fenrir-naru/ninja-scan-light/board/NinjaScanLight2-layout_BOM.png

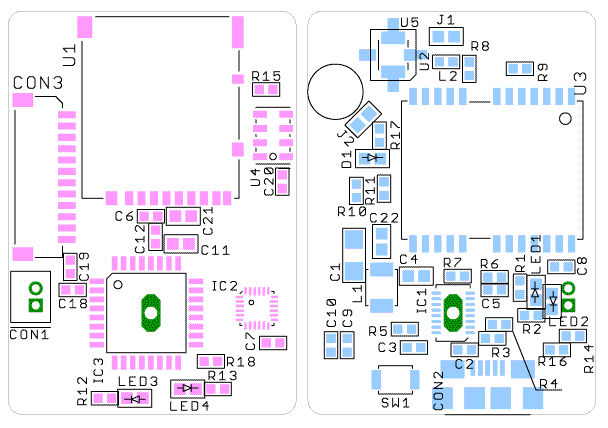
board/NinjaScanLight2-layout_BOM.png
