fenrir-naru/ninja-scan-light/board/NinjaScanLight-layout_BOM.png

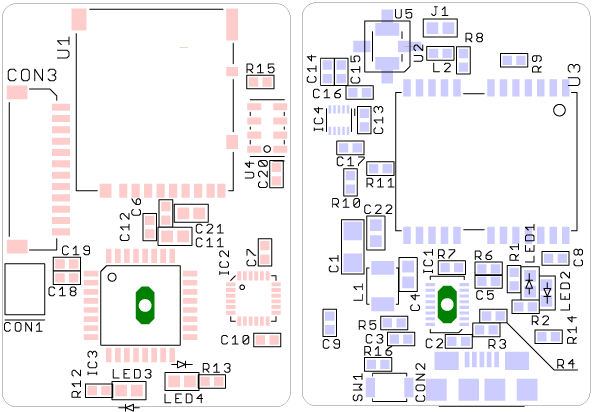
board/NinjaScanLight-layout_BOM.png
