fenrir-naru/ninja-scan-light/board/NinjaScanSlim-layout_BOM.png

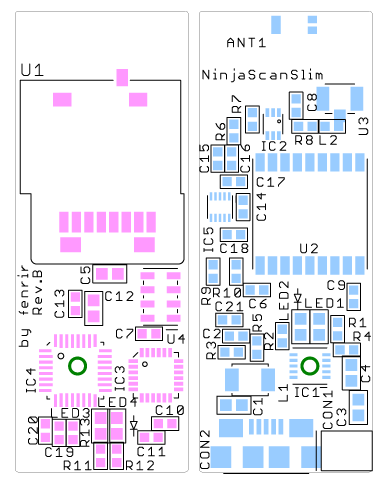
board/NinjaScanSlim-layout_BOM.png
