fenrir-naru/ninja-scan-light/firmware/f38x_uart0.c

/*
 * Copyright (c) 2013, M.Naruoka (fenrir)
 * All rights reserved.
 * 
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
 * THIS SOFTWARE IS PROVIDED BY THE COPYRIGHT HOLDERS AND CONTRIBUTORS "AS IS" 
 * AND ANY EXPRESS OR IMPLIED WARRANTIES, INCLUDING, BUT NOT LIMITED TO, 
 * THE IMPLIED WARRANTIES OF MERCHANTABILITY AND FITNESS FOR A PARTICULAR PURPOSE 
 * ARE DISCLAIMED. IN NO EVENT SHALL THE COPYRIGHT HOLDER OR CONTRIBUTORS 
 * BE LIABLE FOR ANY DIRECT, INDIRECT, INCIDENTAL, SPECIAL, EXEMPLARY, 
 * OR CONSEQUENTIAL DAMAGES (INCLUDING, BUT NOT LIMITED TO, 
 * PROCUREMENT OF SUBSTITUTE GOODS OR SERVICES; 
 * LOSS OF USE, DATA, OR PROFITS; OR BUSINESS INTERRUPTION) 
 * HOWEVER CAUSED AND ON ANY THEORY OF LIABILITY, WHETHER IN CONTRACT, 
 * STRICT LIABILITY, OR TORT (INCLUDING NEGLIGENCE OR OTHERWISE) 
 * ARISING IN ANY WAY OUT OF THE USE OF THIS SOFTWARE, 
 * EVEN IF ADVISED OF THE POSSIBILITY OF SUCH DAMAGE.
 * 
 */

#include <stdio.h>

#include "main.h"
#include "f38x_uart0.h"
#include "fifo.h"

#define DEFAULT_BAUDRATE     9600UL  // Baud rate of UART in bps

#define CRITICAL_UART0(func) \
{\
  ES0 = 0;\
  func;\
  ES0 = 1;\
}

__xdata fifo_char_t fifo_tx0; ///< FIFO TX
__xdata fifo_char_t fifo_rx0; ///< FIFO RX
static __xdata __at (0x000) 
  char buffer_tx0[UART0_TX_BUFFER_SIZE];
static __xdata __at (0x000 + UART0_TX_BUFFER_SIZE) 
  char buffer_rx0[UART0_RX_BUFFER_SIZE];

/**
 * Change UART0 baudrate
 */
static void uart0_bauding_config(u16 baudrate_register){
  
  TR1 = 0;
  do{
    if (baudrate_register < 0x100){
      TH1 = (u8)(~baudrate_register);
      CKCON |=  0x08;  // T1M = 1; SCA1:0 = xx
      break;
    }
    baudrate_register >>= 2; // 1/4
    if (baudrate_register < 0x100){
      TH1 = (u8)(~baudrate_register);
      CKCON &= ~0x0B;
      CKCON |=  0x01;  // T1M = 0; SCA1:0 = 01
      break;
    }
    baudrate_register /= 3; // 1/4*1/3=1/12
    if (baudrate_register < 0x100){
      TH1 = (u8)(~baudrate_register);
      CKCON &= ~0x0B;  // T1M = 0; SCA1:0 = 00
      break;
    }
    baudrate_register >>= 2; // 1/4*1/3*1/4=1/48
    TH1 = (u8)(~baudrate_register);
    CKCON &= ~0x0B;
    CKCON |=  0x02;    // T1M = 0; SCA1:0 = 10
  }while(0);
  
  TL1 = TH1;        // init Timer1
  TMOD &= ~0xf0;    // TMOD: timer 1 in 8-bit autoreload
  TMOD |=  0x20;
  TR1 = 1;
}

#define _uart0_bauding(baudrate, clk) \
  uart0_bauding_config((u16)(clk/2/baudrate))

void uart0_bauding(u32 baudrate){
  _uart0_bauding(baudrate, SYSCLK);
}

/**
 * Initialize UART0
 */
void uart0_init() {
  SCON0 = 0x10;     // SCON0: 8-bit variable bit rate
                    //        level of STOP bit is ignored
                    //        RX enabled
                    //        ninth bits are zeros
                    //        clear RI0 and TI0 bits
  fifo_char_init(&fifo_tx0, buffer_tx0, UART0_TX_BUFFER_SIZE); 
  fifo_char_init(&fifo_rx0, buffer_rx0, UART0_RX_BUFFER_SIZE); 

  _uart0_bauding(DEFAULT_BAUDRATE, SYSCLK);

  TB80 = 0;         // TB80 is used for writing flag. '1' means writing, otherwise '0'.
  ES0 = 1;          // Enable interrupt
  //PS0 = 1;          // Interrupt priority
}

void uart0_init_boot() {
  SCON0 = 0x10;     // SCON0: 8-bit variable bit rate
                    //        level of STOP bit is ignored
                    //        RX enabled
                    //        ninth bits are zeros
                    //        clear RI0 and TI0 bits
  _uart0_bauding(DEFAULT_BAUDRATE, SYSCLK_BOOT);
}

/**
 * Register transmitting data via UART0
 * 
 * @param data pointer to data
 * @param size size of data
 * @return (FIFO_SIZE_T) the size of registered data to buffer
 */
FIFO_SIZE_T uart0_write(char *buf, FIFO_SIZE_T size){
  if(size){
    if(ES0){ // non blocking
      // TB80 is used for writing flag.
      // if '0', which indicates not writing, interrupt must be invoked manually.
      size = fifo_char_write(&fifo_tx0, buf, size);
      CRITICAL_UART0(
        if(!(SCON0 & 0x0A)){ // !TB80 && !TI0
          TI0 = 1; // Manual interrupt
        }
      );
    }else{ // blocking
      FIFO_SIZE_T i = size;
      do{
        SBUF0 = *(buf++);
        while(!TI0);
        TI0 = 0;
      }while(--i);
    }
  }
  return size;
}

/**
 * Return the empty buffer size of data which will be transferred via UART0
 * 
 * @return (FIFO_SIZE_T) the size
 */
FIFO_SIZE_T uart0_tx_margin(){
  return fifo_char_margin(&fifo_tx0);
}

/**
 * Get the received data via UART0
 * 
 * @param buf buffer
 * @param size the size of buffer
 * @return (FIFO_SIZE_T) the real size of grabbed data
 */
FIFO_SIZE_T uart0_read(char *buf, FIFO_SIZE_T size){
  return fifo_char_read(&fifo_rx0, buf, size);
}

/**
 * Return the size of unread data which is received via UART0
 * 
 * @return (FIFO_SIZE_T) the size
 */
FIFO_SIZE_T uart0_rx_size(){
  return fifo_char_size(&fifo_rx0);
}

///< Interrupt(TI0 / RI0)
void interrupt_uart0 () __interrupt (INTERRUPT_UART0) {
  unsigned char res;

  if(RI0){
    RI0 = 0;
    /* push to ring buffer */
    FIFO_DIRECT_PUT(fifo_rx0, SBUF0, res);
    if(res == 0){
      // TODO: buffer overflow
    }
  }

  if(TI0){
    TI0 = 0;
    /* has byte to write? */
    FIFO_DIRECT_GET(fifo_tx0, SBUF0, res);
    if(res > 0){
      TB80 = 1; // TB80 is used as UART0 writing flag. set 1 (writing)
    }else{
      TB80 = 0; // TB80 is used as UART0 writing flag. set 0 (not writing)
    }
  }
}


// stdio.h support

/**
 * putchar - blocking
 */
#if defined(SDCC) && (SDCC >= 370)
int putchar (int c_){
  char c = (char)c_;
#else
void putchar (char c){
#endif
  while(uart0_write(&c, 1) == 0);
}

/**
 * getchar - blocking
 */
#if defined(SDCC) && (SDCC >= 370)
int getchar (void){
#else
char getchar (void){
#endif
  char c;
  while(uart0_read(&c, sizeof(c)) == 0);
  return c;
}
