fenrir-naru/ninja-scan-light/tool/log_CSV.cpp

/*
 * Copyright (c) 2013, M.Naruoka (fenrir)
 * All rights reserved.
 *
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
 * THIS SOFTWARE IS PROVIDED BY THE COPYRIGHT HOLDERS AND CONTRIBUTORS "AS IS"
 * AND ANY EXPRESS OR IMPLIED WARRANTIES, INCLUDING, BUT NOT LIMITED TO,
 * THE IMPLIED WARRANTIES OF MERCHANTABILITY AND FITNESS FOR A PARTICULAR PURPOSE
 * ARE DISCLAIMED. IN NO EVENT SHALL THE COPYRIGHT HOLDER OR CONTRIBUTORS
 * BE LIABLE FOR ANY DIRECT, INDIRECT, INCIDENTAL, SPECIAL, EXEMPLARY,
 * OR CONSEQUENTIAL DAMAGES (INCLUDING, BUT NOT LIMITED TO,
 * PROCUREMENT OF SUBSTITUTE GOODS OR SERVICES;
 * LOSS OF USE, DATA, OR PROFITS; OR BUSINESS INTERRUPTION)
 * HOWEVER CAUSED AND ON ANY THEORY OF LIABILITY, WHETHER IN CONTRACT,
 * STRICT LIABILITY, OR TORT (INCLUDING NEGLIGENCE OR OTHERWISE)
 * ARISING IN ANY WAY OUT OF THE USE OF THIS SOFTWARE,
 * EVEN IF ADVISED OF THE POSSIBILITY OF SUCH DAMAGE.
 *
 */

#if defined(_MSC_VER) && _MSC_VER >= 1400
#define _USE_MATH_DEFINES
//#define _CRT_SECURE_NO_WARNINGS // stop warning recommending secure functions such as sprintf_s
typedef __int64 int64_t;
#endif

#include <iostream>
#include <fstream>
#include <iomanip>
#include <sstream>
#include <exception>

#define IS_LITTLE_ENDIAN 1
#include "SylphideStream.h"
#include "SylphideProcessor.h"

typedef double float_sylph_t;
#include "analyze_common.h"
#include "calibration.h"

using namespace std;

struct Options : public GlobalOptions<float_sylph_t> {
  typedef GlobalOptions<float_sylph_t> super_t;
  enum {
    PAGE_A, PAGE_G, PAGE_F, PAGE_P, PAGE_M, PAGE_N, PAGE_OTHER,
    PAGE_KINDS
  };
  typedef enum {
    PAGE_SELECTED_POSITIVE = 1,
    PAGE_SELECTED_DEFAULT = 0,
    PAGE_SELECTED_NEGATIVE = -1,
  } page_selected_t;
  page_selected_t page_selected[PAGE_KINDS]; // = {PAGE_SELECTED_DEFAULT};

  int page_P_mode, page_F_mode, page_M_mode;
  int debug_level;
  typedef CalendarTime<float_sylph_t> calendar_time_t;
  calendar_time_t::Converter time_gps2local;
  bool use_calendar_time;
  bool as_filter;

  typedef StandardCalibration<float_sylph_t> inertial_conv_t;

  struct {
    bool is_active;
    inertial_conv_t inertial_conv;
  } physical_converter;

  Options() 
      : super_t(),
      page_P_mode(5),
      page_F_mode(3),
      page_M_mode(0),
      debug_level(0),
      time_gps2local(),
      use_calendar_time(false), as_filter(false) {

    physical_converter.is_active = false;
    super_t::set_typical_calibration_specs(physical_converter.inertial_conv);

    for(int i(0); i < PAGE_KINDS; ++i){
      page_selected[i] = PAGE_SELECTED_DEFAULT;
    }
  }
  ~Options(){}
  
  struct formatted_time_t {
    const Options &options;
    float_sylph_t itow;
    friend ostream &operator<<(ostream &out, const formatted_time_t &t){
      if(t.options.use_calendar_time){ // year, month, mday, hour, min, sec
        calendar_time_t t2(
            t.options.time_gps2local.convert(t.itow));
        out << t2.year << ", "
            << t2.month << ", "
            << t2.mday << ", "
            << t2.hour << ", "
            << t2.min << ", "
            << t2.sec;
      }else{
        out << t.itow;
      }
      return out;
    }
  };

  template <class T>
  formatted_time_t format_time(const T &itow){
    formatted_time_t res = {*this, itow};
    return res;
  }

  template <class T>
  bool is_time_in_range(const T &sec) const {
    return super_t::is_time_in_range(sec, time_gps2local.gps_time.wn);
  }
  bool is_time_in_range() const {
    return super_t::is_time_in_range(time_gps2local.gps_time.sec, time_gps2local.gps_time.wn);
  }

  /**
   * Check command argument
   * 
   * @param spec Command
   * @return (bool) If recognized, true; otherwise false
   */
  bool check_spec(const char *spec){
#define CHECK_OPTION(name, novalue, operation, disp) { \
  const char *value(get_value(spec, #name, novalue)); \
  if(value){ \
    {operation;} \
    std::cerr << #name << ": " << disp << std::endl; \
    return true; \
  } \
}
    CHECK_OPTION(page_P_mode, false,
        page_P_mode = atoi(value),
        page_P_mode);
    CHECK_OPTION(page_F_mode, false,
        page_F_mode = atoi(value),
        page_F_mode);
    CHECK_OPTION(page_M_mode, false,
        page_M_mode = atoi(value),
        page_M_mode);
    CHECK_OPTION(page_other, true,
        page_selected[PAGE_OTHER] = is_true(value) ? PAGE_SELECTED_POSITIVE : PAGE_SELECTED_NEGATIVE,
        (page_selected[PAGE_OTHER] > PAGE_SELECTED_DEFAULT ? "on" : "off"));

    do{ // Change time outputs from gpstime[ms] to calendartime(YY,MM,DD,HH,MM,SS) formats
      const char *value(get_value(spec, "calendar_time"));
      if(!value){break;}
      int correction_hr(0);
      if(!is_true(value)){
        correction_hr = atoi(value); // Specify time zone by hour.
      }
      use_calendar_time = true;
      time_gps2local.correction_sec = 60 * 60 * correction_hr;
      cerr << "use_calendar_time: UTC "
          << (correction_hr >= 0 ? '+' : '-')
          << correction_hr << " [hr]" << endl;
      return true;
    }while(false);

    do{
      const char *value(get_value(spec, "page", false));
      if(!value){break;}
      page_selected_t flag(PAGE_SELECTED_POSITIVE);
      if(*value == '-'){
        flag = PAGE_SELECTED_NEGATIVE;
        value++;
      }
      switch(*value){
        case 'A': page_selected[PAGE_A] = flag; break;
        case 'G': page_selected[PAGE_G] = flag; break;
        case 'F': page_selected[PAGE_F] = flag; break;
        case 'M': page_selected[PAGE_M] = flag; break;
        case 'N': page_selected[PAGE_N] = flag; break;
        case 'P': page_selected[PAGE_P] = flag; break;
        default: return false;
      }
      return true;
    }while(false);

    CHECK_OPTION(debug, false,
        debug_level = atoi(value),
        debug_level);
    CHECK_OPTION(as_filter, true,
        as_filter = is_true(value),
        (as_filter ? "on" : "off"));

    CHECK_OPTION(physical, true,
        physical_converter.is_active = is_true(value),
        (physical_converter.is_active ? "on" : "off"));
    CHECK_OPTION(calib_file, false,
        if(!load_calibration_file(physical_converter.inertial_conv, value)){
          return false;
        }, value << " (loaded)" << std::endl << physical_converter.inertial_conv);
#undef CHECK_OPTION
    return super_t::check_spec(spec);
  }
} options;

class StreamProcessor : public SylphideProcessor<float_sylph_t> {
  protected:
    int invoked;
    typedef SylphideProcessor<float_sylph_t> super_t;

    template <class Observer>
    static float_sylph_t get_corrected_ITOW(const Observer &observer){
      float_sylph_t raw_itow(observer.fetch_ITOW());
      if(options.reduce_1pps_sync_error){
        static float_sylph_t previous_itow(0);
        float_sylph_t delta_t(raw_itow - previous_itow);
        if((delta_t >= 1) && (delta_t < 2)){
          raw_itow -= 1;
        }
        previous_itow = raw_itow;
      }
      return raw_itow;
    }
  
  public:
    /**
     * Check A page (AD converted values)
     * 
     * @param observer A page observer
     */
    struct HandlerA {
      int count;
      void (HandlerA::*formatter)(const float_sylph_t &current, const A_Observer_t::values_t &values) const;
      void operator()(const super_t::A_Observer_t &observer){
        if(!observer.validate()){return;} // check validity
        
        float_sylph_t current(StreamProcessor::get_corrected_ITOW(observer));
        if(!options.is_time_in_range(current)){return;}
        
        A_Observer_t::values_t values(observer.fetch_values());
        (this->*formatter)(current, values);
        count++;
      }
      void dump_raw(const float_sylph_t &current, const A_Observer_t::values_t &values) const {
        options.out() 
            << count << ", "
            << options.format_time(current) << ", ";
        
        for(int i(0); i < 8; i++){
          options.out() << values.values[i] << ", ";
        }
        options.out() << values.temperature << endl;
      }
      void dump_physical(const float_sylph_t &current, const A_Observer_t::values_t &values) const {
        options.out()
            << count << ", "
            << options.format_time(current);

        int ch[9];
        for(int i = 0; i < 8; i++){
          ch[i] = values.values[i];
        }
        ch[8] = values.temperature;

        Options::inertial_conv_t::result_t
            accel(options.physical_converter.inertial_conv.raw2accel(ch)),
            omega(options.physical_converter.inertial_conv.raw2omega(ch));

        for(int i(0); i < 3; i++){ // accelerometer[m/s^2]
          options.out() << ", " << accel.values[i];
        }
        for(int i(0); i < 3; i++){ // gyro[deg/sec]
          options.out() << ", " << rad2deg(omega.values[i]);
        }
        options.out() << endl;
      }
      HandlerA() : count(0), formatter(&HandlerA::dump_raw) {}
    } handler_A;
    
    /**
     * Check G page (u-blox GPS receiver output)
     * 
     * @param observer G page observer
     */
    struct HandlerG {
      bool change_0x0102, change_0x0112;
      unsigned int itow_ms_0x0102, itow_ms_0x0112;
      super_t::G_Observer_t::position_t position;
      super_t::G_Observer_t::position_acc_t position_acc;
      super_t::G_Observer_t::velocity_t velocity;
      super_t::G_Observer_t::velocity_acc_t velocity_acc;
      HandlerG() 
          : change_0x0102(false), change_0x0112(false),
          itow_ms_0x0102(0), itow_ms_0x0112(0),
          position(0, 0, 0), position_acc(0, 0),
          velocity(0, 0, 0), velocity_acc(0) {
      }
      ~HandlerG(){}
      
      static void update_time(const super_t::G_Observer_t &observer, const bool &packet_check){
        if(packet_check){
          super_t::G_Observer_t::packet_type_t packet_type(observer.packet_type());
          if((packet_type.mclass != 0x01) || (packet_type.mid != 0x20)){return;}
        }

        // NAV-TIMEGPS
        float_sylph_t itow(observer.fetch_ITOW());
        char buf[4];
        observer.inspect(buf, sizeof(buf), 6 + 8);
        if((unsigned char)buf[3] & 0x02){ // valid week number
          int wn(le_char2_2_num<unsigned short>(*buf));

          if((unsigned char)buf[3] & 0x04){ // valid UTC (leap seconds)
            options.time_gps2local.update(itow, wn, (char)(buf[2]));
          }else{
            options.time_gps2local.update(itow, wn);
          }
        }else{
          options.time_gps2local.update(itow);
        }
      }

      static void test(const super_t::G_Observer_t &observer){
        if(!observer.validate()){return;}

        update_time(observer, true);
      }

      void dump(const unsigned int &itow_ms){
        if(options.page_selected[Options::PAGE_G] <= Options::PAGE_SELECTED_DEFAULT){return;}

        float_sylph_t current(1E-3 * itow_ms);
        if(!options.is_time_in_range(current)){return;}

        options.out() << options.format_time(current) << ", ";
        if(change_0x0102){
          options.out() << position.latitude << ", "
              << position.longitude << ", "
              << position.altitude << ", "
              << position_acc.horizontal << ", "
              << position_acc.vertical << ", ";
        }else{
          options.out() << ", , , , , ";
        }
        if(change_0x0112){
          options.out() << velocity.north << ", "
              << velocity.east << ", "
              << velocity.down << ", "
              << velocity_acc.acc;
        }else{
          options.out() << ", , , ";
        }
        options.out() << endl;
        change_0x0102 = change_0x0112 = false;
      }

      void operator()(const super_t::G_Observer_t &observer){
        if(!observer.validate()){return;}
        
        super_t::G_Observer_t::packet_type_t
            packet_type(observer.packet_type());
        switch(packet_type.mclass){
          case 0x01: {
            switch(packet_type.mid){
              case 0x02:   // NAV-POSLLH
              case 0x14: { // NAV-HPPOSLLH
                unsigned int itow_ms;
                super_t::G_Observer_t::position_t pos;
                super_t::G_Observer_t::position_acc_t pos_acc;
                if(packet_type.mid == 0x14){
                  itow_ms = observer.fetch_ITOW_ms(4);
                  if(itow_ms == itow_ms_0x0102){ // when 0x0102 comes earlier
                    change_0x0102 = false; // accept overwrite with 0x0114
                  }
                  pos = observer.fetch_position_hp();
                  pos_acc = observer.fetch_position_acc_hp();
                }else{
                  itow_ms = observer.fetch_ITOW_ms();
                  if(itow_ms == itow_ms_0x0102){ // when 0x0114 comes earlier
                    break; // skip 0x0102.
                  }
                  pos = observer.fetch_position();
                  pos_acc = observer.fetch_position_acc();
                }

                if(change_0x0102){ // previous position is not dumped
                  dump(itow_ms_0x0102);
                }
                itow_ms_0x0102 = observer.fetch_ITOW_ms();
                position = pos;
                position_acc = pos_acc;
                change_0x0102 = true;
                if(itow_ms_0x0102 == itow_ms_0x0112){ // position and velocity are acquired
                  dump(itow_ms_0x0102);
                }
                break;
              }
              case 0x12: { // NAV-VELNED
                if(change_0x0112){ // previous velocity is not dumped
                  dump(itow_ms_0x0112);
                }
                itow_ms_0x0112 = observer.fetch_ITOW_ms();
                velocity = observer.fetch_velocity();
                velocity_acc = observer.fetch_velocity_acc();
                change_0x0112 = true;
                if(itow_ms_0x0102 == itow_ms_0x0112){ // position and velocity are acquired
                  dump(itow_ms_0x0112);
                }
                break;
              }
              case 0x20: { // NAV-TIMEGPS
                update_time(observer, false);
                break;
              }
            }
            break;
          }
          default:
            break;
        }
      }
    } handler_G;
    
    /**
     * check F page (FPGA output), which is not used for NinjaScan
     * 
     * @param observer F page observer
     */
    struct HandlerF {
      int count;
      HandlerF() : count(0) {}
      void operator()(const F_Observer_t &observer){
        if(!observer.validate()){return;}
        
        float_sylph_t current(StreamProcessor::get_corrected_ITOW(observer));
        if(!options.is_time_in_range(current)){return;}
        
        options.out() << (count++)
             << ", " << options.format_time(current);
        
        F_Observer_t::values_t values(observer.fetch_values());
        for(int i = 0; i < 8; i++){
          //if(values.servo_in[i] < 1000){values.servo_in[i] += 1000;}
          if(options.page_F_mode & 0x01){ // bit 0 for input
            options.out() << ", " << values.servo_in[i];
          }
          if(options.page_F_mode & 0x02){ // bit 1 for output
            options.out() << ", " << values.servo_out[i];
          }
        }
        options.out() << endl;
      }
    } handler_F;
    
    
    struct HandlerP {
      void (HandlerP::*formatter)(
          const float_sylph_t &current, const int &index,
          const Int32 &pressure, const Int32 &temperature) const;

      static void ms5XXX_convert(
          const Int32 &d1, const Int32 &d2, const Uint16 (&coef)[6],
          Int32 &dT, Int32 &temperature, int64_t &off, int64_t &sens){
        dT = d2 - (coef[4] << 8);
        temperature = (Int32)2000 + (((int64_t)dT * coef[5]) >> 23);

        off = ((int64_t)coef[1] << 16) + (((int64_t)coef[3] * dT) >> 7);
        sens = ((int64_t)coef[0] << 15) + (((int64_t)coef[2] * dT) >> 8);
      }
      static void ms5611_convert(
          const Int32 &d1, const Int32 &d2,
          Int32 &pressure, Int32 &temperature,
          const Uint16 (&coef)[6]){
        Int32 dT;
        int64_t off, sens;
        ms5XXX_convert(d1, d2, coef, dT, temperature, off, sens);

        // Figure 3
        if(temperature < 2000){
          Int32 t2(((int64_t)dT * dT) >> 31);
          Int32 dT2(temperature - 2000), dT2_2(dT2 * dT2);
          Int32 off2((dT2_2 * 5) >> 1);
          Int32 sens2((dT2_2 * 5) >> 2);
          if(temperature < -1500){
            Int32 dT3(temperature + 1500), dT3_2(dT3 * dT3);
            off2 += dT3_2 * 7;
            sens2 += (dT3_2 * 11) >> 1;
          }
          temperature -= t2;
          off -= off2;
          sens -= sens2;
        }

        pressure = (Int32)(((((int64_t)d1 * sens) >> 21) - off) >> 15);
      }
      static void ms5803_01_convert(
          const Int32 &d1, const Int32 &d2,
          Int32 &pressure, Int32 &temperature,
          const Uint16 (&coef)[6]){
        Int32 dT;
        int64_t off, sens;
        ms5XXX_convert(d1, d2, coef, dT, temperature, off, sens);

        // Figure 16
        if(temperature < 2000){
          Int32 t2(((int64_t)dT * dT) >> 31);
          Int32 dT2(temperature - 2000), dT2_2(dT2 * dT2);
          Int32 off2(dT2_2 * 3);
          Int32 sens2((dT2_2 * 7) >> 3);
          if(temperature < -1500){
            Int32 dT3(temperature + 1500), dT3_2(dT3 * dT3);
            sens2 += (dT3_2 * 2);
          }
          temperature -= t2;
          off -= off2;
          sens -= sens2;
        }else if(temperature >= 4500){
          Int32 dT2(temperature - 4500), dT2_2(dT2 * dT2);
          Int32 sens2(-(dT2_2 >> 3));
          sens -= sens2;
        }

        pressure = (Int32)(((((int64_t)d1 * sens) >> 21) - off) >> 15);
      }
      static void ms5803_30_convert(
          const Int32 &d1, const Int32 &d2,
          Int32 &pressure, Int32 &temperature,
          const Uint16 (&coef)[6]){
        Int32 dT;
        int64_t off, sens;
        ms5XXX_convert(d1, d2, coef, dT, temperature, off, sens);

        // Figure 16
        Int32 dT2(temperature - 2000), dT2_2(dT2 * dT2);
        if(temperature < 2000){
          Int32 t2(((int64_t)dT * dT * 3) >> 33);
          Int32 off2((dT2_2 * 3) >> 1);
          Int32 sens2((dT2_2 * 7) >> 3);
          if(temperature < -1500){
            Int32 dT3(temperature + 1500), dT3_2(dT3 * dT3);
            off2 += (dT3_2 * 7);
            sens2 += (dT3_2 * 4);
          }
          temperature -= t2;
          off -= off2;
          sens -= sens2;
        }else{
          Int32 t2(((int64_t)dT * dT * 7) >> 37);
          Int32 off2(dT2_2 >> 4);
          temperature -= t2;
          off -= off2;
        }

        pressure = (Int32)(((((int64_t)d1 * sens) >> 21) - off) >> 13) * 10;
      }

      /**
       * check P page (pressure sensor)
       * 
       * @param observer F page observer
       */
      void operator()(const P_Observer_t &observer){
        if(!observer.validate()){return;}
        
        float_sylph_t current(StreamProcessor::get_corrected_ITOW(observer));
        if(!options.is_time_in_range(current)){return;}
        
        switch(options.page_P_mode){
          case 5: // MS5611 with coefficients
          case 6: // MS5803-01 with coefficients
          case 7: { // MS5803-30 with coefficients
            Uint16 coef[6];
            char buf[sizeof(Uint16)];
            for(int i(0); i < sizeof(coef) / sizeof(coef[0]); i++){
              observer.inspect(&buf[0], sizeof(buf), 19 + (sizeof(buf) * i));
              coef[i] = be_char2_2_num<Uint16>(*buf);
            }

            for(int i(0), j(-1); i < 2; i++, j++){
              char buf[2][4];
              buf[0][0] = buf[1][0] = 0;
              observer.inspect(&buf[0][1], 3, 7 + 6 * i);
              observer.inspect(&buf[1][1], 3, 10 + 6 * i);
              Uint32
                  d1(be_char4_2_num<Uint32>(buf[0][0])),
                  d2(be_char4_2_num<Uint32>(buf[1][0]));
              Int32 pressure, temperature;

              void (*converter[])(
                  const Int32 &d1, const Int32 &d2,
                  Int32 &pressure, Int32 &temperature,
                  const Uint16 (&coef)[6]) = {
                ms5611_convert, ms5803_01_convert, ms5803_30_convert,
              };
              (*(converter[options.page_P_mode - 5]))(d1, d2, pressure, temperature, coef);
              (this->*formatter)(current, j, pressure, temperature);
            }
            break;
          }
        }
      }
      void dump_raw(
          const float_sylph_t &current, const int &index,
          const Int32 &pressure, const Int32 &temperature) const {
        options.out()
            << options.format_time(current) << ", " << index << ", "
            << pressure << ", " << temperature << endl;
      }
      void dump_physical(
          const float_sylph_t &current, const int &index,
          const Int32 &pressure, const Int32 &temperature) const {
        options.out()
            << options.format_time(current) << ", " << index << ", "
            << (float_sylph_t)pressure << ", "  // [Pa]
            << (float_sylph_t)temperature / 100 << endl; // [degC]
      }
      HandlerP() : formatter(&HandlerP::dump_raw) {}
    } handler_P;
    
    /**
     * check M page (magnetic sensor)
     * 
     * @param observer M page observer
     */
    struct HandlerM {
      void (HandlerM::*formatter)(const float_sylph_t &current, const M_Observer_t::values_t &values) const;
      void operator()(const M_Observer_t &observer){
        if(!observer.validate()){return;}
        
        float_sylph_t current(StreamProcessor::get_corrected_ITOW(observer));
        if(!options.is_time_in_range(current)){return;}
        
        M_Observer_t::values_t values(observer.fetch_values());

        switch(options.page_M_mode){
          case 1: // -atan2(y, x)した結果[deg]を表示
            for(int i(0), j(-3); i < 4; i++, j++){
              options.out() << options.format_time(current) << ", "
                   << j << ", "
                   << rad2deg(-atan2((double)values.y[i], (double)values.x[i])) << endl;
            }
            break;
          default:
            (this->*formatter)(current, values);
        }
      }
      void dump_raw(const float_sylph_t &current, const M_Observer_t::values_t &values) const {
        for(int i(0), j(-3); i < 4; i++, j++){
          options.out() << options.format_time(current) << ", "
               << j << ", "
               << values.x[i] << ", "
               << values.y[i] << ", "
               << values.z[i] << endl;
        }
      }
      void dump_physical(const float_sylph_t &current, const M_Observer_t::values_t &values) const {
        /* TODO how to resolve the difference of sensors;
         *
         * [ver1] MAG3110 => scale factor is 0.10 uT / LSB
         * [ver2] AK8963 in MPU9250 => scale factor is 0.15 uT / LSB (16-bit mode @see mpu9250.c)
         */
        dump_raw(current, values);
      }
      HandlerM() : formatter(&HandlerM::dump_raw) {}
    } handler_M;

    /**
     * check N page (navigation information), which is not used for NinjaScan
     * 
     * @param observer M page observer
     */
    struct HandlerN {
      void operator()(const N_Observer_t &observer){
        if(!observer.validate()){return;}
        
        float_sylph_t current(StreamProcessor::get_corrected_ITOW(observer));
        if(!options.is_time_in_range(current)){return;}
        
        switch(observer.kind()){
          case 0: {
            N_Observer_t::navdata_t values(observer.fetch_navdata());
            
            options.out() << options.format_time(values.itow) << ", "
                << values.longitude << ", "
                << values.latitude << ", "
                << values.altitude << ", "
                << values.v_north << ", "
                << values.v_east << ", "
                << values.v_down << ", "
                << values.heading << ", "
                << values.pitch << ", "
                << values.roll << endl;
            break;
          }
          default:
            return;
        }
      }
    } handler_N;

#if 0
    /**
     * checker for C page in SylphideProtocol format
     *
     */
    class SylphideStreamHandler
        : public Sylphide_Packet_Observer<float_sylph_t> {
      protected:
        typedef Sylphide_Packet_Observer<float_sylph_t> super_t;
        typedef SylphideStreamHandler self_t;
      public:
        bool previous_seek;
        unsigned int invoked;
        SylphideStreamHandler()
            : super_t(SYLPHIDE_PAGE_SIZE),
            previous_seek(false), invoked(0) {}
        ~SylphideStreamHandler() {}

        /**
         * callback function when packet is found
         *
         */
        void operator()(const self_t &observer){
          if(!observer.validate()){return;}

        }
    } handler_C;
#endif
    
    /**
     * check X page (ADS122[0] or ELVR[1])
     *
     * @param observer X page observer
     */
    struct HandlerX : public Data24Bytes_Packet_Observer<float_sylph_t> {
      typedef Data24Bytes_Packet_Observer<float_sylph_t> super_t;

      bool previous_seek;
      unsigned int invoked;
      void (HandlerX::*formatter)(const float_sylph_t &current) const;

      void operator()(const HandlerX &observer){
        if(!observer.validate()){return;}
        float_sylph_t current(StreamProcessor::get_corrected_ITOW(observer));
        if(!options.is_time_in_range(current)){return;}
        (this->*formatter)(current);
      }
      super_t::u32_t get_3bytesBE(const int &index) const {
        super_t::v8_t buf[sizeof(super_t::u32_t)] = {0};
        this->inspect(&buf[1], 3, 7 + (3 * index));
        return be_char4_2_num<super_t::u32_t>(buf[0]);
      }
      void dump_ad122_raw(const float_sylph_t &current) const {
        for(int i(-1), k(0); i <= 0; i++){
          options.out() << options.format_time(current) << ", " << i;
          for(int j(0); j < 4; ++j){
            options.out() << ", " << get_3bytesBE(k++);
          }
          options.out() << endl;
        }
      }
      void dump_ad122_physical(const float_sylph_t &current) const {
        for(int i(-1), k(0); i <= 0; i++){
          options.out() << options.format_time(current) << ", " << i;
          for(int j(0); j < 3; ++j){ // voltage
            options.out() << ", "
                << (float_sylph_t)get_3bytesBE(k++) / (1 << (23 - 11)) / 1000;
            // 0x800000 = (1 << 23), Vref = 2.048V
          }
          { // temperature
            super_t::u32_t v(get_3bytesBE(k++) >> 10);
            options.out() << ", " << (float_sylph_t)(((v & 0x2000) ? -(int)0x4000 : (int)0) + v) / 32;
          }
          options.out() << endl;
        }
      }
      super_t::u16_t get_2bytesBE(const int &index) const {
        super_t::v8_t buf[sizeof(super_t::u16_t)] = {0};
        this->inspect(buf, 2, 7 + (2 * index));
        return be_char2_2_num<super_t::u16_t>(buf[0]);
      }
      void dump_as_elvr_raw(const float_sylph_t &current) const {
        for(int i(-11), j(0); i <= 0; ++i, ++j){
          options.out()
              << options.format_time(current) << ", "
              << i << ", " << get_2bytesBE(j) << endl;
        }
      }
      void dump_as_elvr_physical(const float_sylph_t &current) const {
        dump_as_elvr_raw(current); // TODO
      }
      void dump_raw(const float_sylph_t &current) const {
        switch((int)((*this)[0])){
          case 1:
            return dump_as_elvr_raw(current);
          default:
            return dump_ad122_raw(current);
        }
      }
      void dump_physical(const float_sylph_t &current) const {
        switch((int)((*this)[0])){
          case 1:
            return dump_as_elvr_physical(current);
          default:
            return dump_ad122_physical(current);
        }
      }
      HandlerX()
          : super_t(SYLPHIDE_PAGE_SIZE),
          previous_seek(false), invoked(0),
          formatter(&HandlerX::dump_raw) {}
      ~HandlerX() {}
    } handler_X;
    
  public:
    StreamProcessor()
        : super_t(SYLPHIDE_PAGE_SIZE * 0x100), invoked(0) {
      
    }
    ~StreamProcessor(){}
    
    void process_pages(char *buf, const int &buf_size){
      switch(buf[0]){
#define assign_case_cnd(type, mark, cnd) \
case mark: if(cnd){ \
  super_t::process_packet( \
      buf, buf_size, \
      observer_ ## type, previous_seek_next_ ## type, handler_ ## type); \
} \
break;
#define assign_case(type, mark) \
    assign_case_cnd(type, mark, options.page_selected[Options::PAGE_ ## type] > Options::PAGE_SELECTED_DEFAULT)
        assign_case(A, 'A');
        assign_case_cnd(G, 'G', true);
        assign_case(F, 'F');
        assign_case(P, 'P');
        assign_case(M, 'M');
        assign_case(N, 'N');
#undef assign_case
#undef assign_case_cnd
#if 0
          case 'C': if(options.page_selected[Options::PAGE_C] > Options::PAGE_SELECTED_DEFAULT){
            super_t::process_packet(
                buf, buf_size,
                handler_C, handler_C.previous_seek, handler_C);
          }
          break;
#endif
        default: if(options.page_selected[Options::PAGE_OTHER] > Options::PAGE_SELECTED_DEFAULT){
          if(buf[0] == 'X'){
            super_t::process_packet(
                buf, buf_size,
                handler_X, handler_X.previous_seek, handler_X);
          }else if(buf[0] == 'T'){
            stringstream ss;
            ss << hex;
            for(int i(0); i < buf_size; i++){
              ss << setfill('0')
                  << setw(2)
                  << (unsigned int)((unsigned char)buf[i]) << ' ';
            }
            ss << endl;
            options.out() << ss.str();
          }
        }
        break;
      }
    }

    void filter_pages(char *buf, const int &buf_size){
      switch(buf[0]){
#define filter_page(type, mark) \
case mark: if(options.page_selected[Options::PAGE_ ## type] < Options::PAGE_SELECTED_DEFAULT){return;} break;
        filter_page(A, 'A');
        filter_page(F, 'F');
        filter_page(P, 'P');
        filter_page(M, 'M');
        filter_page(N, 'N');
#undef filter_page
        case 'G':
          super_t::process_packet(
              buf, buf_size,
              observer_G, previous_seek_next_G, HandlerG::test);
          if(options.page_selected[Options::PAGE_G] < Options::PAGE_SELECTED_DEFAULT){return;}
          break;
        default:
          if(options.page_selected[Options::PAGE_OTHER] < Options::PAGE_SELECTED_DEFAULT){return;}
          break;
      }
      if(!options.is_time_in_range()){return;}
      options.out().write(buf, buf_size);
    }

    /**
     * Extract packet from stream until the end of stream is found
     * 
     * @param in stream
     */
    void process(istream &in){
      char buffer[SYLPHIDE_PAGE_SIZE];
      
      if(options.physical_converter.is_active){
        handler_A.formatter = &HandlerA::dump_physical;
        handler_P.formatter = &HandlerP::dump_physical;
        handler_M.formatter = &HandlerM::dump_physical;
        handler_X.formatter = &HandlerX::dump_physical;
        cerr << "Units are [m/s^2], [deg/s], [Pa], [degC], and [V] "
            "for acceleration, angular speed, pressure, temperature, and voltage respectively."
            << endl;
      }

      void (StreamProcessor::*task)(char *, const int &)(&StreamProcessor::process_pages);
      if(options.as_filter){
#if defined(_MSC_VER) || defined(__CYGWIN__)
        if(&(options.out()) == &(std::cout)){
          setmode(fileno(stdout), O_BINARY); // change binary mode explicitly
        }
#endif
        task = &StreamProcessor::filter_pages;
      }

      int read_count;
      while(true){
        in.read(buffer, SYLPHIDE_PAGE_SIZE);
        read_count = in.gcount();
        if(in.fail() || (read_count == 0)){return;}
        invoked++;
      
        if(options.debug_level){
          cerr << "--read-- : " << invoked << " page" << endl;
          cerr << hex;
          for(int i(0); i < read_count; i++){
            cerr << setfill('0') 
                << setw(2)
                << (unsigned int)((unsigned char)buffer[i]) << ' ';
          }
          cerr << dec;
          cerr << endl;
          
          if(read_count < SYLPHIDE_PAGE_SIZE){
            cerr << "--skipped-- : " << invoked << " page ; count = " << read_count << endl;
          }
        }
      
        (this->*task)(buffer, read_count);
      }
    }
};

int main(int argc, char *argv[]){

  cerr << "NinjaScan converter to make CSV format data." << endl;
  cerr << "Usage: " << argv[0] << " [options, ex) --page=A] log.dat" << endl;
  if(argc < 2){
    cerr << "Error: too few arguments; " << argc << " < min(2)" << endl;
    return -1;
  }
  
  // For backward compatibility
  if(strstr(argv[0], "log_AD_CSV") == argv[0]){
    options.page_selected[Options::PAGE_A] = Options::PAGE_SELECTED_POSITIVE;
  }else if(strstr(argv[0], "log_F_CSV") == argv[0]){
    options.page_selected[Options::PAGE_F] = Options::PAGE_SELECTED_POSITIVE;
  }else if(strstr(argv[0], "log_M_CSV") == argv[0]){
    options.page_selected[Options::PAGE_M] = Options::PAGE_SELECTED_POSITIVE;
  }else if(strstr(argv[0], "log_P_CSV") == argv[0]){
    options.page_selected[Options::PAGE_P] = Options::PAGE_SELECTED_POSITIVE;
  }
  
  StreamProcessor processor;
  
  int log_index(1); // log file name is assumed to be given by argv[1]
  
  // check options
  for(int i(1); i < argc; i++){
    if(options.check_spec(argv[i])){continue;}
    // if arg is not an option, assume arg as log file name
    if(log_index != 1){ // Detect unknown option by multiple substitution to log_index.
      cerr << "Unknown option!! : " << argv[i] << endl;
      return -1;
    }
    log_index = i;
  }
  
  options.out().precision(10);
  if(options.in_sylphide){
    SylphideIStream sylph_in(options.spec2istream(argv[log_index]), SYLPHIDE_PAGE_SIZE);
    processor.process(sylph_in);
  }else{
    processor.process(options.spec2istream(argv[log_index]));
  }
  
  return 0;
}
