fenrir-naru/ninja-scan-light/tool/INS_GPS.cpp

/**
 * @file INS/GPS post-processor for NinjaScan
 *
 */

/*
 * Copyright (c) 2016, M.Naruoka (fenrir)
 * All rights reserved.
 *
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
 * THIS SOFTWARE IS PROVIDED BY THE COPYRIGHT HOLDERS AND CONTRIBUTORS "AS IS"
 * AND ANY EXPRESS OR IMPLIED WARRANTIES, INCLUDING, BUT NOT LIMITED TO,
 * THE IMPLIED WARRANTIES OF MERCHANTABILITY AND FITNESS FOR A PARTICULAR PURPOSE
 * ARE DISCLAIMED. IN NO EVENT SHALL THE COPYRIGHT HOLDER OR CONTRIBUTORS
 * BE LIABLE FOR ANY DIRECT, INDIRECT, INCIDENTAL, SPECIAL, EXEMPLARY,
 * OR CONSEQUENTIAL DAMAGES (INCLUDING, BUT NOT LIMITED TO,
 * PROCUREMENT OF SUBSTITUTE GOODS OR SERVICES;
 * LOSS OF USE, DATA, OR PROFITS; OR BUSINESS INTERRUPTION)
 * HOWEVER CAUSED AND ON ANY THEORY OF LIABILITY, WHETHER IN CONTRACT,
 * STRICT LIABILITY, OR TORT (INCLUDING NEGLIGENCE OR OTHERWISE)
 * ARISING IN ANY WAY OUT OF THE USE OF THIS SOFTWARE,
 * EVEN IF ADVISED OF THE POSSIBILITY OF SUCH DAMAGE.
 *
 */

/*
 * === Quick guide ===
 *
 * This program is used to analyze data gathered with NinjaScan logger
 * by using Kalman filter based integrated navigation technology
 * called INS/GPS, which stands for inertial navigation system (INS)
 * and global positioning system (GPS).
 * The program outputs position (longitude, latitude, and WGS84 altitude),
 * velocity (north, east, and down), and attitude (true heading, roll and pitch angles)
 * with a time stamp.
 *
 * It is briefly technically noted that this program utilizes loosely-coupled INS/GPS algorithm,
 * which implies at least four GPS satellites must be available to output the results.
 * In addition, this program is not suitable to be used for real-time application.
 * This is because its processing strategy is post-process, that is, the data is sorted
 * in time-series order before application of the INS/GPS algorithm,
 * in order to compensate for the output delay of a GPS receiver installed on the logger.
 *
 * Its usage is
 *   INS_GPS [option(s)] <log.dat>,
 * where <log.dat> is a mandatory parameter pointing to a log file stored in a logger.
 * There are some reserved values for <log.dat>; If <log.dat> equals to - (hyphen),
 * the program will try to read log data from the standard input.
 * Or, when <log.dat> is COMx for Windows or /dev/ttyACMx for *NIX,
 * the program will try to read data from the specified serial port.
 *
 * The [option(s)] is optional parameter(s).
 * If multiple parameters are specified, they should be separated by space.
 * The representative parameters are the followings;
 *
 *   --start_gpst=(GPS time in week [sec])
 *      specifies start GPS time for INS/GPS post-process.
 *   --start_gpst=(GPS week):(GPS time in week [sec])
 *      specifies start GPS week and time for INS/GPS post-process.
 *
 *   --end_gpst=(GPS time in week [sec])
 *      specifies end GPS time for INS/GPS post-process.
 *   --end_gpst=(GPS week):(GPS time in week [sec])
 *      specifies end GPS week and time for INS/GPS post-process.
 *
 *   --dump_update=<on|off>
 *      specifies whether the program outputs results when inertial information is obtained
 *      (so called, results for time update), or not. Its default is on.
 *   --dump_correct=<off|on>
 *      specifies whether the program outputs results when information processed by a GPS receiver
 *      is obtained, (so called, results for measurement update) or not. Its default is off.
 *   --dump_relative[=(latitude[deg]),(longitude(deg))]
 *      additionally generates relative horizontal positions respect to the base position in meter.
 *      If this option is specified without latitude and longitude, the initial position is used
 *      as its base position. Its default is off.
 *
 *   --calendar_time
 *      changes time stamp of output from (internal) GPS time of week (default)
 *      to year, month, day of month, hour, minute, and second.
 *
 *   --init_attitude_deg=(heading [deg]),(pitch [deg]),(roll [deg])
 *      specifies initial true heading, pitch and roll angles. Their default values are
 *      computed by using Earth magnetic force and gravity observed with magnetic sensor
 *      and accelerometer, respectively, under the assumption that the logger may be stationary
 *      at the beginning. While the default initial pitch and roll angles can be approximately
 *      true because Earth's gravity is comparatively large, the default true heading is not
 *      so reliable because magnetic field is easily disturbed by surrounding metal objects
 *      or electric current. Therefore, to specify the initial heading angle is strongly
 *      recommended. Please also check the next --init_yaw_deg option, which only specifies
 *      the initial heading angle.
 *   --init_yaw_deg=(heading [deg])
 *      specifies initial true heading in degree. Please also refer the above explanation
 *      about --init_attitude_deg.
 *
 *   --est_bias=<on|off>
 *      specifies whether the mechanism to estimate sensor bias drift is utilized, or not.
 *      The default is on.
 *   --use_udkf=<off|on>
 *      specifies whether the UD factorized Kalamn filter (UDKF), or the standard Kalman
 *      filter is utilized. The default is off (standard KF).
 *
 *   --direct_sylphide=<off|on>
 *   --in_sylphide=<off|on>
 *      specifies whether the format of the input log file follows Sylphide protocol or not.
 *      The default is off. Please use this option with "on" value when the program directly read
 *      data from the NinjaScan logger in USB CDC Mode.
 *
 *   --gps_init_acc_2d=(sigma [m])
 *   --gps_init_acc_v=(sigma [m])
 *   --gps_cont_acc_2d=(sigma [m])
 *      specify initial measurement update threshold for GPS 2D estimated error,
 *      initial measurement update threshold for GPS vertical estimated error,
 *      and continual measurement update threshold for GPS 2D estimated error, respectively.
 *      These default values are 20, 10, and 100, respectively.
 *
 * The followings are advanced (i.e., very experimental) options;
 *   --back_propagate
 *      apply Kalman filter smoothing to previously time-updated data
 *      (exclusive with --realtime)
 *   --realtime
 *      change GPS synchronization strategy to support realtime applications.
 *      It processes data without sorting and outputs calculation results as quick as possible.
 *      (exclusive with --back_propagate)
 *
 */

// Comment-In when QNAN DEBUG
//#include <float.h>
//unsigned int fp_control_state = _controlfp(_EM_INEXACT, _MCW_EM);

#include <iostream>
#include <sstream>
#include <iomanip>
#include <string>
#include <exception>

#include <cstdio>
#include <cmath>
#include <cstring>
#include <cctype>

#include <vector>
#include <list>
#include <utility>
#include <deque>
#include <algorithm>

#define IS_LITTLE_ENDIAN 1
#include "SylphideStream.h"
#include "SylphideProcessor.h"

typedef double float_sylph_t;

#include "param/matrix.h"
#include "param/vector3.h"
#include "param/quaternion.h"
#include "param/complex.h"

template <>
struct Vector3Data_TypeMapper<float_sylph_t> {
  typedef Vector3Data_NoFlyWeight<float_sylph_t> res_t;
};
template <>
struct QuaternionData_TypeMapper<float_sylph_t> {
  typedef QuaternionData_NoFlyWeight<float_sylph_t> res_t;
};

#include "algorithm/kalman.h"

#include "navigation/INS_GPS_Factory.h"
#include "navigation/INS_GPS_Synchronization.h"
#include "navigation/INS_GPS_Debug.h"

#include "navigation/WGS84.h"
#include "navigation/MagneticField.h"

#include "analyze_common.h"
#include "calibration.h"

struct Options : public GlobalOptions<float_sylph_t> {
  typedef GlobalOptions<float_sylph_t> super_t;

  // Output
  bool dump_update; ///< True for dumping states at time updates
  bool dump_correct; ///< True for dumping states at measurement updates
  bool dump_stddev; ///< True for dumping standard deviations
  struct dump_relative_t {
    enum mode_t {MODE_INACTIVE, MODE_BASE_UNSET, MODE_ACTIVE} mode;
    typedef NAVData<float_sylph_t>::RelativePosition pos_t;
    pos_t::base_t base;
    dump_relative_t() : mode(MODE_INACTIVE), base() {}
    void set_base(const float_sylph_t &lat, const float_sylph_t &lng){
      if(mode != MODE_BASE_UNSET){return;}
      base.lat_zero = lat;
      base.lat_sf = WGS84Generic<float_sylph_t>::R_meridian(lat);
      base.lng_zero = lng;
      base.lng_sf = WGS84Generic<float_sylph_t>::R_normal(lat) * std::cos(lat);
      mode = MODE_ACTIVE;
    }
    friend std::ostream &operator<<(std::ostream &out, const dump_relative_t &rel){
      switch(rel.mode){
        case MODE_BASE_UNSET:
          out << "on (base position will be initialized)";
          break;
        case MODE_ACTIVE:
          out << "on, base(lat,lng)=("
              << rad2deg(rel.base.lat_zero) << ',' << rad2deg(rel.base.lng_zero) << ')';
          break;
      }
      return out;
    }
    void parse_spec(const char *spec){
      mode = MODE_BASE_UNSET;
      if(is_true(spec)){return;}
      double dummy[2];
      if(std::sscanf(spec, "%lf,%lf", &dummy[0], &dummy[1]) == 2){
        set_base(deg2rad(bounds(dummy[0], 90)), deg2rad(bounds(dummy[1], 180)));
      }else{
        std::cerr << "Invalid spec for --dump_relative[=lat,lng]: " << spec << std::endl;
        exit(-1);
      }
    }
    void label(std::ostream &out) const {
      pos_t::label(out);
    }
    pos_t operator()(const NAVData<float_sylph_t> &nav){
      return nav.relative_position(base);
    }
    operator bool() const {
      return mode != MODE_INACTIVE;
    }
  } dump_relative; ///< Controller for relative (2D) position outputs  bool out_is_N_packet; ///< True for NPacket formatted outputs
  bool out_is_N_packet; ///< True for NPacket formatted outputs

  // Time Stamp
  struct time_stamp_t {
    enum mode_t {
      ITOW,
      CALENDAR_TIME,
    } mode;
    int correction_hr;
    time_stamp_t()
        : mode(ITOW), correction_hr(0) {}
    friend std::ostream &operator<<(std::ostream &out, const time_stamp_t &stamp){
      switch(stamp.mode){
        case CALENDAR_TIME:
          out << "UTC";
          if(stamp.correction_hr != 0){
            out << (stamp.correction_hr > 0 ? " +" : " ")
                << stamp.correction_hr << " [hr]";
          }
          break;
      }
      return out;
    }
    void parse_calendar_spec(const char *spec){
      mode = CALENDAR_TIME;
      if(is_true(spec)){return;}
      char *spec_end;
      correction_hr = std::strtol(spec, &spec_end, 10);
      if(spec == spec_end){
        std::cerr << "Invalid spec for --calendar_time[=(+/-hr)]: " << spec << std::endl;
        exit(-1);
      }
    }
  } time_stamp;

  // Navigation strategies
  enum {
    INS_GPS_SYNC_OFFLINE,
    INS_GPS_SYNC_BACK_PROPAGATION, ///< a.k.a, smoothing
    INS_GPS_SYNC_REALTIME,
  } ins_gps_sync_strategy;
  bool est_bias; ///< True for performing bias estimation
  bool use_udkf; ///< True for UD Kalman filtering
  bool use_egm; ///< True for precise Earth gravity model

  INS_GPS_Back_Propagate_Property<float_sylph_t> back_propagate_property;
  INS_GPS_RealTime_Property<float_sylph_t> realttime_property;

  // GPS options
  bool gps_fake_lock; ///< true when dummy GPS data is used.
  struct gps_threshold_t {
    float_sylph_t init_acc_2d; ///< Initial measurement update threshold for GPS 2D estimated error
    float_sylph_t init_acc_v;  ///< Initial measurement update threshold for GPS vertical estimated error
    float_sylph_t cont_acc_2d; ///< Continual measurement update threshold for GPS 2D estimated error
    gps_threshold_t()
        : init_acc_2d(20.), init_acc_v(10.),
        cont_acc_2d(100.) {}
  } gps_threshold;

  // Magnetic sensor
  bool use_magnet; ///< True for utilizing magnetic sensor
  float_sylph_t mag_heading_accuracy_deg; ///< Accuracy of magnetic sensor in degrees
  float_sylph_t yaw_correct_with_mag_when_speed_less_than_ms; ///< Threshold for yaw compensation; performing it when under this value [m/s], or ignored non-positive values

  // Manual initialization
  struct initial_attitude_t {
    float_sylph_t yaw_deg, pitch_deg, roll_deg; ///< Initial attitude [deg] (yaw, pitch, roll)
    enum mode_t {NOT_GIVEN = 0, YAW_ONLY = 1, YAW_PITCH = 2, FULL_GIVEN = 3} mode; ///< Whether initial attitude is given.
    initial_attitude_t()
        : yaw_deg(0), pitch_deg(0), roll_deg(0),
        mode(NOT_GIVEN) {}
    initial_attitude_t &parse(const char *spec){
      int converted(std::sscanf(spec, "%lf,%lf,%lf",
          &yaw_deg, &pitch_deg, &roll_deg));
      if(converted > 0){mode = (mode_t)converted;}
      return *this;
    }
    initial_attitude_t &parse_yaw(const char *spec){
      yaw_deg = std::atof(spec);
      mode = YAW_ONLY;
      return *this;
    }
    friend std::ostream &operator<<(std::ostream &out, const initial_attitude_t &atti){
      return out << "(yaw, pitch, roll) (args:"
          << atti.mode << "): "
          << atti.yaw_deg << ", "
          << atti.pitch_deg << ", "
          << atti.roll_deg;
    }
  } initial_attitude;
  std::istream *init_misc; ///< other manual initialization
  std::stringstream init_misc_buf; ///< buffer for init_misc string

  // Debug
  INS_GPS_Debug_Property<float_sylph_t> debug_property;

  Options()
      : super_t(),
      dump_update(true), dump_correct(false), dump_stddev(false), dump_relative(),
      out_is_N_packet(false),
      time_stamp(),
      ins_gps_sync_strategy(INS_GPS_SYNC_OFFLINE),
      est_bias(true), use_udkf(false), use_egm(false),
      back_propagate_property(),
      realttime_property(),
      gps_fake_lock(false), gps_threshold(),
      use_magnet(false),
      mag_heading_accuracy_deg(3),
      yaw_correct_with_mag_when_speed_less_than_ms(5),
      initial_attitude(),
      init_misc_buf(), init_misc(&init_misc_buf),
      debug_property() {
    realttime_property.rt_mode = INS_GPS_RealTime_Property<float_sylph_t>::RT_LIGHT_WEIGHT;
  }
  ~Options(){}

  /**
   * Check spec
   * 
   * @param spec command
   * @return (bool) true when consumed, otherwise false
   */
  bool check_spec(const char *spec){

    const char *key;
    const unsigned int key_length(get_key(spec, &key));
    if(key_length == 0){return super_t::check_spec(spec);}

    bool key_checked(false);

#define CHECK_KEY(name) \
  (key_checked \
    || (key_checked = ((key_length == std::strlen(#name)) \
        && (std::strncmp(key, #name, key_length) == 0))))
#define CHECK_ALIAS(name) CHECK_KEY(name)
#define CHECK_OPTION(name, accept_no_value, operation, disp) { \
  while(CHECK_KEY(name)){ \
    key_checked = false; \
    const char *value(get_value(spec, key_length, accept_no_value)); \
    if((!accept_no_value) && (!value)){return false;} \
    {operation;} \
    std::cerr << #name << ": " << disp << std::endl; \
    return true; \
  } \
}
#define CHECK_OPTION_BOOL(target) \
CHECK_OPTION(target, true, target = is_true(value), (target ? "on" : "off"));

    CHECK_ALIAS(dump-update);
    CHECK_OPTION_BOOL(dump_update);
    CHECK_ALIAS(dump-correct);
    CHECK_OPTION_BOOL(dump_correct);
    CHECK_OPTION_BOOL(dump_stddev);
    CHECK_OPTION(dump_relative, true,
        dump_relative.parse_spec(value),
        dump_relative);
    CHECK_ALIAS(out_N_packet);
    CHECK_OPTION_BOOL(out_is_N_packet);

    CHECK_OPTION(calendar_time, true,
        time_stamp.parse_calendar_spec(value),
        time_stamp);

    CHECK_OPTION(back_propagate, true,
        if(is_true(value)){ins_gps_sync_strategy = INS_GPS_SYNC_BACK_PROPAGATION;},
        (ins_gps_sync_strategy == INS_GPS_SYNC_BACK_PROPAGATION ? "on" : "off"));
    CHECK_OPTION(realtime, true,
        if(is_true(value)){ins_gps_sync_strategy = INS_GPS_SYNC_REALTIME;},
        (ins_gps_sync_strategy == INS_GPS_SYNC_REALTIME ? "on" : "off"));
    CHECK_OPTION_BOOL(est_bias);
    CHECK_OPTION_BOOL(use_udkf);
    CHECK_OPTION_BOOL(use_egm);
    CHECK_OPTION(bp_depth, false,
        back_propagate_property.back_propagate_depth = std::atof(value),
        back_propagate_property.back_propagate_depth);

    CHECK_ALIAS(fake_lock);
    CHECK_OPTION_BOOL(gps_fake_lock);
    CHECK_OPTION(gps_init_acc_2d, false,
        gps_threshold.init_acc_2d = std::atof(value),
        gps_threshold.init_acc_2d << " [m]");
    CHECK_OPTION(gps_init_acc_v, false,
        gps_threshold.init_acc_v = std::atof(value),
        gps_threshold.init_acc_v << " [m]");
    CHECK_OPTION(gps_cont_acc_2d, false,
        gps_threshold.cont_acc_2d = std::atof(value),
        gps_threshold.cont_acc_2d << " [m]");

    CHECK_OPTION_BOOL(use_magnet);
    CHECK_OPTION(mag_heading_accuracy_deg, false,
        mag_heading_accuracy_deg = std::atof(value),
        mag_heading_accuracy_deg << " [deg]");
    CHECK_OPTION(yaw_correct_with_mag_when_speed_less_than_ms, false,
        yaw_correct_with_mag_when_speed_less_than_ms = std::atof(value),
        yaw_correct_with_mag_when_speed_less_than_ms << " [m/s]");

    CHECK_ALIAS(init-attitude-deg);
    if(CHECK_KEY(init_attitude_deg)){
      const char *value(get_value(spec, key_length, false));
      if(!value){return false;}
      std::cerr.write(key, key_length)
          << " " << initial_attitude.parse(value) << std::endl;
      return true;
    }
    CHECK_ALIAS(init-yaw-deg);
    CHECK_OPTION(init_yaw_deg, false,
        initial_attitude.parse_yaw(value),
        initial_attitude.yaw_deg << " [deg]");
    CHECK_OPTION(init_misc, false,
        {init_misc_buf << value << std::endl; return true;},
        "");
    CHECK_OPTION(init_misc_fname, false,
        {std::cerr << "Checking... "; init_misc = &spec2istream(value);},
        value);

    CHECK_OPTION(debug, false,
        if(!debug_property.check_debug_property_spec(value)){break;},
        debug_property.show_debug_property());
#undef CHECK_OPTION
    
    return super_t::check_spec(spec);
  }
} options;

template <class FloatT>
struct CalendarTimeStamp : public CalendarTime<FloatT> {
  typedef CalendarTime<FloatT> super_t;
#if defined(__GNUC__) && (__GNUC__ < 5)
  typedef typename super_t::float_t float_t;
#else
  using typename super_t::float_t;
#endif
  float_t itow;
  CalendarTimeStamp &operator=(const float_t &t){
    super_t::year = super_t::month = super_t::mday = super_t::hour = super_t::min = 0;
    super_t::sec = itow = t;
    return *this;
  }
  CalendarTimeStamp(const super_t &t1, const float_t &t2)
      : super_t(t1), itow(t2) {}
  CalendarTimeStamp(const float_t &t = 0) : super_t(), itow(t) {
    operator=(t);
  }
  operator float_t() const {return itow;}
  static struct label_t {
    friend std::ostream &operator<<(std::ostream &out, const label_t &){
      return out << "year" << ','
          << "month" << ','
          << "day" << ','
          << "hour" << ','
          << "min" << ','
          << "sec";
    }
  } label;
  friend std::ostream &operator<<(std::ostream &out, const CalendarTimeStamp &time){
    return out << time.year << ','
        << time.month << ','
        << time.mday << ','
        << time.hour << ','
        << time.min << ','
        << time.sec;
  }
};
template <class FloatT>
typename CalendarTimeStamp<FloatT>::label_t CalendarTimeStamp<FloatT>::label;

struct A_Packet;
struct G_Packet;
struct M_Packet;
struct TimePacket;

struct Updatable {
  virtual ~Updatable() {}
  virtual void update(const A_Packet &){}
  virtual void update(const G_Packet &){}
  virtual void update(const M_Packet &){}
  virtual void update(const TimePacket &){}
} updatable_blackhole;

class NAV : public Updatable {
  public:
    typedef NAVData<float_sylph_t> data_t;
    typedef std::vector<const data_t *> updated_items_t;
    virtual ~NAV(){}
  public:
    virtual void label(std::ostream &out) const = 0;
    virtual updated_items_t updated_items() const {
      return updated_items_t();
    }
    virtual void inspect(std::ostream &out) const {}
    virtual float_sylph_t &operator[](const unsigned &index) = 0;

    template <class Container>
    static typename Container::const_iterator nearest(
        const Container &packets_time_series, const float_sylph_t &itow,
        const unsigned int &group_size = 1){
      typename Container::const_iterator
          it_head(packets_time_series.begin()),
          it_eval(it_head + (group_size / 2)),
          it_end(packets_time_series.end());
      for(int i(distance(it_head, it_end));
          i > (int)group_size;
          i--, it_head++, it_eval++){
        if(it_eval->itow >= itow){break;}
      }
      return it_head;
    }

    /**
     * Estimate yaw correction angle by using magnetic sensor values
     *
     * @param attitude
     * @return yaw correction angle [rad]
     */
    static float_sylph_t get_mag_delta_yaw(
        const Vector3<float_sylph_t> &mag,
        const Quaternion<float_sylph_t> &attitude,
        const float_sylph_t &latitude, const float_sylph_t &longitude, const float_sylph_t &altitude){

      typedef Vector3<float_sylph_t> vec_t;
      typedef Quaternion<float_sylph_t> quat_t;

      // Cancel attitude (inverted)
      vec_t mag_horizontal((attitude * quat_t(0, mag) * attitude.conj()).vector());

      // Call Earth's magnetic field model
      MagneticField::field_components_res_t mag_model(
          MagneticField::field_components(IGRF12::IGRF2015,
              latitude, longitude, altitude));
      vec_t mag_field(mag_model.north, mag_model.east, mag_model.down);

      // Get the correction angle with the model
      return std::atan2(mag_field[1], mag_field[0])
          - std::atan2(mag_horizontal[1], mag_horizontal[0]);
    }

    float_sylph_t get_mag_delta_yaw(
        const Vector3<float_sylph_t> &mag,
        const Quaternion<float_sylph_t> &attitude,
        const data_t &data){

      return get_mag_delta_yaw(mag, attitude, data.latitude(), data.longitude(), data.height());
    }

    float_sylph_t get_mag_delta_yaw(
        const Vector3<float_sylph_t> &mag,
        const data_t &data){

      return get_mag_delta_yaw(mag,
          INS<float_sylph_t>::euler2q(data.euler_psi(), data.euler_theta(), data.euler_phi()),
          data.latitude(), data.longitude(), data.height());
    }

    /**
     * Estimate yaw angle
     *
     */
    static float_sylph_t get_mag_yaw(
        const Vector3<float_sylph_t> &mag,
        const float_sylph_t &pitch, const float_sylph_t &roll,
        const float_sylph_t &latitude, const float_sylph_t &longitude, const float_sylph_t &altitude){

      return get_mag_delta_yaw(
          mag,
          INS<float_sylph_t>::euler2q(0, pitch, roll),
          latitude, longitude, altitude);
    }

    float_sylph_t get_mag_yaw(
        const Vector3<float_sylph_t> &mag,
        const data_t &data){

      return get_mag_yaw(
          mag,
          data.euler_theta(), data.euler_phi(),
          data.latitude(), data.longitude(), data.height());
    }
};

template <class BaseNAV>
struct NAV_Factory {
  typedef BaseNAV self_t;

  struct NAVDisplay : public BaseNAV {
    NAVDisplay() : BaseNAV() {}
    void label(std::ostream &out = std::cout) const {
      if(options.out_is_N_packet){return;}
      BaseNAV::label(options.out());
      if(options.dump_relative){options.dump_relative.label(options.out() << ',');}
      options.out() << std::endl;
    }
    void updated() const {
      const NAV::updated_items_t &items(BaseNAV::updated_items());
      if(items.empty()){return;}

      if(options.out_is_N_packet){
        char buf[SYLPHIDE_PAGE_SIZE];
        items.back()->encode_N0(buf);
        options.out().write(buf, sizeof(buf));
      }else{
        for(NAV::updated_items_t::const_iterator it(items.begin()), it_end(items.end());
            it != it_end; ++it){
          options.out() << (**it);
          if(options.dump_relative){
            options.out() << ',' << options.dump_relative(**it);
          }
          options.out() << std::endl;
        }
      }

      options.out_debug() << items.back()->time_stamp() << ',';
      BaseNAV::inspect(options.out_debug());
      options.out_debug() << std::endl;
    }
#define update_func(type) \
virtual void update(const type &packet){ \
  BaseNAV::update(packet); \
  updated(); \
}
    update_func(A_Packet);
    update_func(G_Packet);
    update_func(M_Packet);
#undef update_func
  };

  typedef NAVDisplay disp_t;
};

/**
 * Base class of log data, which has time stamp.
 */
struct Packet{
  virtual ~Packet() {}
  virtual void apply(NAV &nav) const = 0;

  float_sylph_t itow;

  /**
   * Get interval time between another one
   *
   * @param another
   * @return if another is bigger, positive number will be returned.
   */
  float_sylph_t interval(const Packet &another) const {
    return another.itow - itow;
  }
  static bool compare(const Packet *a, const Packet *b) {
    return a->itow < b->itow;
  }
  /**
   * Get interval time between another one
   * in consideration of one week roll over
   *
   * @param another
   * @return The returned value ranges [-one_week/2, +one_week/2)
   * if another is bigger, positive number will be returned.
   */
  float_sylph_t interval_rollover(const Packet &another) const {
    float_sylph_t delta(another.itow - itow);
    static const int one_week(60 * 60 * 24 * 7);
    return delta - (std::floor((delta / one_week) + 0.5) * one_week);
  }
  static bool compare_rollover(const Packet *a, const Packet *b) {
    return a->interval_rollover(*b) > 0;
  }
};

template <class T>
struct BasicPacket : public Packet {
  void apply(NAV &nav) const {
    nav.update(static_cast<const T &>(*this));
  }
};

/**
 * Inertial and temperature sensor data (ADC raw value)
 */
struct A_Packet : public BasicPacket<A_Packet> {
  Vector3<float_sylph_t> accel; ///< Acceleration
  Vector3<float_sylph_t> omega; ///< Angular speed
};

/**
 * GPS data
 */
struct G_Packet
    : public BasicPacket<G_Packet>,
    public GPS_Solution<float_sylph_t> {
  Vector3<float_sylph_t> *lever_arm;

  G_Packet() : GPS_Solution<float_sylph_t>(), lever_arm(NULL) {}
};

/**
 * Magnetic sensor data
 */
struct M_Packet : public BasicPacket<M_Packet> {
  Vector3<float_sylph_t> mag;
};

struct TimePacket : public BasicPacket<TimePacket> {
  typedef BasicPacket<TimePacket> super_t;
  int week_num, leap_sec;
  bool valid_week_num, valid_leap_sec;
  using super_t::apply;
  template <class FloatT>
  void apply(typename CalendarTime<FloatT>::Converter &converter) const {
    valid_week_num
        ? (valid_leap_sec
            ? converter.update(super_t::itow, week_num, leap_sec)
            : converter.update(super_t::itow, week_num))
        : converter.update(super_t::itow);
  }
};

template <class INS_GPS>
class INS_GPS_NAVData;

template <class INS_GPS>
class INS_GPS_NAV : public NAV {
  public:
    typedef INS_GPS ins_gps_t;
    typedef typename ins_gps_t::float_t float_t;
    typedef typename ins_gps_t::mat_t mat_t;
    typedef typename ins_gps_t::vec3_t vec3_t;
    class Helper;
  protected:
    ins_gps_t *ins_gps;
    Helper helper;

    void setup_filter(void *){}

    template <class BaseINS, template <class> class Filter>
    void setup_filter(Filtered_INS2<BaseINS, Filter> *) {
      /**
       * Initialization of matrix P, system covariance matrix, of Kalman filter.
       * orthogonal elements are
       *  0-2 : initial velocity variance in N, E, D axes, [m/s^2]^2
       *  3-5 : initial variance of position on the Earth which is represented by a delta quaternion
       *        composed of latitude, longitude, and wander azimuth angle.
       *        For instance, 1E-8 is a sufficiently big value.
       *  6   : initial altitude variance [m]^2
       *  7-9 : initial attitude variance represented by a delta quaternion
       *        composed of yaw, pitch, and roll angles.
       *        default values are sufficiently big.
       */
      {
        mat_t P(ins_gps->getFilter().getP());

        P(0, 0) = P(1, 1) = P(2, 2) = 1E+1;
        P(3, 3) = P(4, 4) = P(5, 5) = 1E-8;
        P(6, 6) = 1E+2;
        P(7, 7) = P(8, 8) = 1E-4; // mainly for roll, pitch. 1-sigma about 1 deg.
        P(9, 9) = 5E-3; // mainly for heading. 1-sigma about 7 deg.

        ins_gps->getFilter().setP(P);
      }

      /**
       * Initialization of matrix Q, input covariance matrix, of Kalman filter.
       * orthogonal elements are
       *  0-2 : accelerometer output variance in X, Y, Z axes, [m/s^2]^2
       *  3-5 : angular speed output variance in X, Y, Z axes, [rad/s]^2
       *  6   : gravity variance [m/s^2]^2, normally set small value, such as 1E-6
       */
      {
        mat_t Q(ins_gps->getFilter().getQ());
        
        Q(0, 0) = Q(1, 1) = Q(2, 2) = 25E-4;
        Q(3, 3) = Q(4, 4) = Q(5, 5) = 25E-6;
        Q(6, 6) = 1E-6; //1E-14
        
        ins_gps->getFilter().setQ(Q);
      }
    }

    void setup_filter(
        const vec3_t &accel_sigma,
        const vec3_t &gyro_sigma,
        void *) {}

    template <class BaseINS, template <class> class Filter>
    void setup_filter(
        const vec3_t &accel_sigma,
        const vec3_t &gyro_sigma,
        Filtered_INS2<BaseINS, Filter> *) {

      mat_t Q(ins_gps->getFilter().getQ());
      for(int i(0), j(3); i < 3; i++, j++){
        Q(i, i) = pow(accel_sigma[i], 2);
        Q(j, j) = pow(gyro_sigma[i], 2);
      }
      ins_gps->getFilter().setQ(Q);
    }

    template <class BaseFINS>
    void setup_filter(Filtered_INS_BiasEstimated<BaseFINS> *) {

      setup_filter((BaseFINS *)ins_gps);

      {
        mat_t P(ins_gps->getFilter().getP());
        static const unsigned NP(
            Filtered_INS_BiasEstimated<BaseFINS>::P_SIZE_WITHOUT_BIAS);
        P(NP,     NP)     = P(NP + 1, NP + 1) = P(NP + 2, NP + 2) = 1E-4; // for accelerometer bias drift
        P(NP + 3, NP + 3) = P(NP + 4, NP + 4) = P(NP + 5, NP + 5) = 1E-7; // for gyro bias drift
        ins_gps->getFilter().setP(P);
      }

      {
        mat_t Q(ins_gps->getFilter().getQ());
        static const unsigned NQ(
            Filtered_INS_BiasEstimated<BaseFINS>::Q_SIZE_WITHOUT_BIAS);
        Q(NQ,     NQ)     = Q(NQ + 1, NQ + 1) = Q(NQ + 2, NQ + 2) = 1E-6; // for accelerometer bias drift
        Q(NQ + 3, NQ + 3) = Q(NQ + 4, NQ + 4) = Q(NQ + 5, NQ + 5) = 1E-8; // for gyro bias drift
        ins_gps->getFilter().setQ(Q);
      }

      ins_gps->beta_accel() *= 0.1;
      ins_gps->beta_gyro() *= 0.1; //mems_g.BETA;
    }

    template <class Base_INS_GPS>
    void setup_filter(INS_GPS_Back_Propagate<Base_INS_GPS> *){
      setup_filter((Base_INS_GPS *)ins_gps);
      ins_gps->setup_back_propagation(options.back_propagate_property);
    }

    template <class Base_INS_GPS>
    void setup_filter(INS_GPS_RealTime<Base_INS_GPS> *){
      setup_filter((Base_INS_GPS *)ins_gps);
      ins_gps->setup_realtime(options.realttime_property);
    }

    template <class Base_INS_GPS>
    void setup_filter(INS_GPS_Debug<Base_INS_GPS> *){
      setup_filter((Base_INS_GPS *)ins_gps);
      ins_gps->setup_debug(options.debug_property);
    }

  public:
    INS_GPS_NAV()
        : NAV(),
        ins_gps(new INS_GPS()), helper(*this) {
      setup_filter(ins_gps);
    }
    virtual ~INS_GPS_NAV() {
      delete ins_gps;
    }

    void setup_filter(
        const vec3_t &accel_sigma,
        const vec3_t &gyro_sigma){
      setup_filter(accel_sigma, gyro_sigma, ins_gps);
    }

    void inspect(std::ostream &out, void *) const {}
    template <class INS_GPS_base>
    void inspect(std::ostream &out, INS_GPS_Debug<INS_GPS_base> *) const {
      ins_gps->inspect(out);
    }
    void inspect(std::ostream &out) const {
      inspect(out, ins_gps);
    }

  protected:
    static bool set_matrix_full(mat_t &mat, const char *spec){
      char *_spec(const_cast<char *>(spec)), *_spec2;
      for(unsigned int i(0), i_end(mat.rows()); i < i_end; i++){
        for(unsigned int j(0), j_end(mat.columns()); j < j_end; j++){
          mat(i, j) = std::strtod(_spec2 = _spec, &_spec);
          if(_spec == _spec2){return false;} // No conversion
        }
      }
      return true;
    }
    static bool set_matrix_diagonal(mat_t &mat, const char *spec){
      char *_spec(const_cast<char *>(spec)), *_spec2;
      for(unsigned int i(0), i_end(mat.rows()); i < i_end; i++){
        mat(i, i) = std::strtod(_spec2 = _spec, &_spec);
        if(_spec == _spec2){return false;} // No conversion
      }
      return true;
    }
    static bool set_matrix_1element(mat_t &mat, const char *spec){
      char *_spec(const_cast<char *>(spec)), *_spec2;
      int i((int)std::strtol(_spec2 = _spec, &_spec, 10));
      if(_spec == _spec2){return false;} // No conversion
      int j((int)std::strtol(_spec2 = _spec, &_spec, 10));
      if(_spec == _spec2){return false;} // No conversion
      mat(i, j) = std::strtod(_spec2 = _spec, &_spec);
      return (_spec != _spec2);
    }

    bool init_misc(const char *line, void *){
      return false;
    }
    bool init_misc(const char *line, INS<float_t> *){
      const char *value;
      if(value = Options::get_value2(line, "x")){
        char *spec(const_cast<char *>(value)), *spec2;
        int i((int)std::strtol(spec2 = spec, &spec, 10));
        if(spec == spec2){return false;} // No conversion
        (*ins_gps)[i] = std::strtod(spec2 = spec, &spec);
        return spec != spec2;
      }
      return false;
    }
    template <class BaseINS, template <class> class Filter>
    bool init_misc(const char *line, Filtered_INS2<BaseINS, Filter> *){
      const char *value;
      bool res;

      while(true){
        mat_t P(ins_gps->getFilter().getP());
        if(value = Options::get_value2(line, "P")){
          res = set_matrix_full(P, value);
        }else if(value = Options::get_value2(line, "P_diag")){
          res = set_matrix_diagonal(P, value);
        }else if(value = Options::get_value2(line, "P_elm")){
          res = set_matrix_1element(P, value);
        }else{break;}
        ins_gps->getFilter().setP(P);
        return res;
      }

      while(true){
        mat_t Q(ins_gps->getFilter().getQ());
        if(value = Options::get_value2(line, "Q")){
          res = set_matrix_full(Q, value);
        }else if(value = Options::get_value2(line, "Q_diag")){
          res = set_matrix_diagonal(Q, value);
        }else if(value = Options::get_value2(line, "Q_elm")){
          res = set_matrix_1element(Q, value);
        }else{break;}
        ins_gps->getFilter().setQ(Q);
        return res;
      }

      return init_misc(line, (BaseINS *)ins_gps);
    }

  public:
    bool init_misc(const char *line){
      if(std::strlen(line) == 0){return true;}

      bool res(init_misc(line, ins_gps));
      if(res){
        std::cerr << "Init (misc): " << line << std::endl;
      }
      return res;
    }
    
    float_t &operator[](const unsigned &index){return ins_gps->operator[](index);}
    
    NAV &update(
        const vec3_t &accel,
        const vec3_t &gyro,
        const float_t &elapsedT){
      ins_gps->update(accel, gyro, elapsedT);
      return *this;
    }
  
  public:
    NAV &correct(const G_Packet &gps){
      ins_gps->correct(gps);
      return *this;
    }

    NAV &correct(
        const G_Packet &gps,
        const vec3_t &lever_arm_b,
        const vec3_t &omega_b2i_4b){
      ins_gps->correct(gps, lever_arm_b, omega_b2i_4b);
      return *this;
    }

  protected:
    bool setup_correct(const float_t &advanceT, void *){
      return true;
    }

    template <class INS_GPS_orig>
    bool setup_correct(const float_t &advanceT, INS_GPS_RealTime<INS_GPS_orig> *){
      return ins_gps->setup_correct(advanceT);
    }

  public:
    NAV &correct(
        const G_Packet &gps,
        const float_t &advanceT){
      if(setup_correct(advanceT, ins_gps)){
        return correct(gps);
      }else{
        return *this;
      }
    }

    NAV &correct(
        const G_Packet &gps,
        const vec3_t &lever_arm_b,
        const vec3_t &omega_b2i_4b,
        const float_t &advanceT){
      if(setup_correct(advanceT, ins_gps)){
        return correct(gps, lever_arm_b, omega_b2i_4b);
      }else{
        return *this;
      }
    }

    NAV &correct_yaw(const float_t &delta_yaw){
      ins_gps->correct_yaw(delta_yaw, pow(deg2rad(options.mag_heading_accuracy_deg), 2));
      return *this;
    }
    
    void label(std::ostream &out) const {
      ins_gps->label(out);
    }

    updated_items_t updated_items() const {
      return helper.updated_items();
    }

    void update(const A_Packet &packet){
      helper.before_any_update();
      helper.time_update(packet);
    }
    void update(const G_Packet &packet){
      helper.before_any_update();
      helper.measurement_update(packet);
    }
    void update(const M_Packet &packet){
      helper.before_any_update();
      helper.compass(packet);
    }
    void update(const TimePacket &packet){
      helper.t_stamp_generator.update(packet);
    }
};

template <class INS_GPS>
struct INS_GPS_NAV_Factory : public NAV_Factory<INS_GPS> {

  template <class Calibration>
  static NAV *generate(const Calibration &calibration){
    typedef INS_GPS_NAV_Factory<INS_GPS_NAV<INS_GPS> > nav_t;
    typename nav_t::disp_t *res(new typename nav_t::disp_t());
    res->setup_filter(calibration.sigma_accel().values, calibration.sigma_gyro().values);
    return res;
  }

  private:
  template <class T>
  struct Checker {
    template <class Calibration>
    static NAV *check_covariance(const Calibration &calibration){
      typedef INS_GPS_Debug_Property<float_sylph_t> prop_t;
      switch(options.debug_property.debug_target){
        case prop_t::DEBUG_KF_P:
        case prop_t::DEBUG_KF_FULL:
          return INS_GPS_NAV_Factory<INS_GPS_Debug_Covariance<T> >::generate(calibration);
        case prop_t::DEBUG_NONE:
        default:
          return INS_GPS_NAV_Factory<T>::generate(calibration);
      }
    }

    template <class Calibration>
    static NAV *check_synchronization(const Calibration &calibration){
      switch(options.ins_gps_sync_strategy){
        case Options::INS_GPS_SYNC_BACK_PROPAGATION:
          return Checker<INS_GPS_Back_Propagate<T> >::check_covariance(calibration);
        case Options::INS_GPS_SYNC_REALTIME:
          return Checker<INS_GPS_RealTime<T> >::check_covariance(calibration);
        case Options::INS_GPS_SYNC_OFFLINE:
        default:
          return check_covariance(calibration);
      }
    }

    template <class Calibration>
    static NAV *check_navdata(const Calibration &calibration){
      return Checker<INS_GPS_NAVData<T> >::check_synchronization(calibration);
    }

    template <class Calibration>
    static NAV *check_pure_ins(const Calibration &calibration){
      typedef INS_GPS_Debug_Property<float_sylph_t> prop_t;
      return (options.debug_property.debug_target == prop_t::DEBUG_PURE_INERTIAL)
          ? Checker<INS_GPS_Debug_PureInertial<T> >::check_navdata(calibration)
          : check_navdata(calibration);
    }
  };

  template <class T>
  struct Checker<INS_GPS_Debug_PureInertial<T> > {
    template <class Calibration>
    static NAV *check_navdata(const Calibration &calibration){
      return options.dump_stddev ?
          INS_GPS_NAV_Factory<
              INS_GPS_NAVData<INS_GPS_Debug_PureInertial<T, typename T::filtered_ins_t> >
            >::generate(calibration) :
          INS_GPS_NAV_Factory<
              INS_GPS_NAVData<INS_GPS_Debug_PureInertial<T> >
            >::generate(calibration);
    }
  };

  public:
  template <class Calibration>
  static NAV *get_nav(const Calibration &calibration){
    return Checker<INS_GPS>::check_pure_ins(calibration);
  }
};

template <class PureINS, class TimeStamp = typename PureINS::float_t>
class INS_NAVData : public PureINS, public NAVData<typename PureINS::float_t> {
  public:
    typedef NAVData<typename PureINS::float_t> super_data_t;
    typedef TimeStamp time_stamp_t;
  protected:
    mutable const char *mode;
    mutable time_stamp_t itow;
  public:
    INS_NAVData() : PureINS(), mode("N/A"), itow(0) {}
    INS_NAVData(const INS_NAVData<PureINS, time_stamp_t> &orig, const bool &deepcopy = false)
        : PureINS(orig, deepcopy), mode(orig.mode), itow(orig.itow) {}
    ~INS_NAVData(){}
#define MAKE_PROXY_FUNC(fname) \
typename PureINS::float_t fname() const {return PureINS::fname();}
    MAKE_PROXY_FUNC(longitude);
    MAKE_PROXY_FUNC(latitude);
    MAKE_PROXY_FUNC(height);
    MAKE_PROXY_FUNC(v_north);
    MAKE_PROXY_FUNC(v_east);
    MAKE_PROXY_FUNC(v_down);
    MAKE_PROXY_FUNC(heading);
    MAKE_PROXY_FUNC(euler_phi);
    MAKE_PROXY_FUNC(euler_theta);
    MAKE_PROXY_FUNC(euler_psi);
    MAKE_PROXY_FUNC(azimuth);
#undef MAKE_PROXY_FUNC
    typename PureINS::float_t time_stamp() const {return (typename PureINS::float_t)itow;}

    void set_header(const char *_mode) const {
      mode = _mode;
    }
    void set_header(const char *_mode, const time_stamp_t &_itow) const {
      mode = _mode;
      itow = _itow;
    }

    static struct label_time_t {
      template <class T>
      static std::ostream &label(std::ostream &out, T){
        return out << "itow";
      }
      template <class FloatT>
      static std::ostream &label(std::ostream &out, const CalendarTimeStamp<FloatT> &){
        return out << CalendarTimeStamp<FloatT>::label;
      }
      friend std::ostream &operator<<(std::ostream &out, const label_time_t &){
        return label(out, time_stamp_t());
      }
    } label_time;

    void label(std::ostream &out) const {
      out << "mode" << ','
          << label_time << ',';
      super_data_t::label(out);
    }
    void dump(std::ostream &out) const {
      out << mode << ','
          << itow << ',';
      super_data_t::dump(out);
    }
};
template <class PureINS, class TimeStamp>
typename INS_NAVData<PureINS, TimeStamp>::label_time_t
    INS_NAVData<PureINS, TimeStamp>::label_time;

template <class INS_GPS>
class INS_GPS_NAVData : public INS_GPS {
  public:
#if defined(__GNUC__) && (__GNUC__ < 5)
    typedef typename INS_GPS::vec3_t vec3_t;
    typedef typename INS_GPS::mat_t mat_t;
#else
    using typename INS_GPS::vec3_t;
    using typename INS_GPS::mat_t;
#endif
  public:
    INS_GPS_NAVData() : INS_GPS() {}
    INS_GPS_NAVData(const INS_GPS_NAVData<INS_GPS> &orig, const bool &deepcopy = false)
        : INS_GPS(orig, deepcopy) {}
    ~INS_GPS_NAVData(){}
  protected:
    static void label2(std::ostream &out, const void *){}

    template <class BaseINS, template <class> class Filter>
    static void label2(std::ostream &out, const Filtered_INS2<BaseINS, Filter> *fins){
      label2(out, (const BaseINS *)fins);
      if(options.dump_stddev){
        out << ',' << "s1(longitude)"
            << ',' << "s1(latitude)"
            << ',' << "s1(height)"
            << ',' << "s1(v_north)"
            << ',' << "s1(v_east)"
            << ',' << "s1(v_down)"
            << ',' << "s1(psi)"
            << ',' << "s1(theta)"
            << ',' << "s1(phi)";
        if(options.dump_relative){
          out << ',' << "s1(east_west)"
              << ',' << "s1(north_south)";
        }
      }
    }

    template <class BaseINS>
    static void label2(std::ostream &out, const INS_BiasEstimated<BaseINS> *ins){
      label2(out, (const BaseINS *)ins);
      out << ',' << "bias_accel(X)"   //Bias
          << ',' << "bias_accel(Y)"
          << ',' << "bias_accel(Z)"
          << ',' << "bias_gyro(X)"
          << ',' << "bias_gyro(Y)"
          << ',' << "bias_gyro(Z)" ;
    }

    template <class BaseFINS>
    static void label2(std::ostream &out, const Filtered_INS_BiasEstimated<BaseFINS> *fins){
      label2(out, (const BaseFINS *)fins);
      if(options.dump_stddev){
        out << ',' << "s1(bias_accel(X))"
            << ',' << "s1(bias_accel(Y))"
            << ',' << "s1(bias_accel(Z))"
            << ',' << "s1(bias_gyro(X))"
            << ',' << "s1(bias_gyro(Y))"
            << ',' << "s1(bias_gyro(Z))";
      }
    }
  public:
    /**
     * print label
     */
    void label(std::ostream &out) const {
      INS_GPS::label(out);
      label2(out, this);
    }
  
  protected:
    void dump2(std::ostream &out, const void *) const {}

    template <class BaseINS, template <class> class Filter>
    void dump2(std::ostream &out, const Filtered_INS2<BaseINS, Filter> *fins) const {
      dump2(out, (const BaseINS *)fins);
      if(options.dump_stddev){
        typename Filtered_INS2<BaseINS, Filter>::StandardDeviations sigma(fins->getSigma());
        out << ',' << rad2deg(sigma.longitude_rad)
            << ',' << rad2deg(sigma.latitude_rad)
            << ',' << sigma.height_m
            << ',' << sigma.v_north_ms
            << ',' << sigma.v_east_ms
            << ',' << sigma.v_down_ms
            << ',' << rad2deg(sigma.heading_rad)
            << ',' << rad2deg(sigma.pitch_rad)
            << ',' << rad2deg(sigma.roll_rad);
        if(options.dump_relative){
          out << ',' << options.dump_relative.base.relative_east_west(sigma.longitude_rad)
              << ',' << options.dump_relative.base.relative_north_south(sigma.latitude_rad);
        }
      }
    }

    template <class BaseINS>
    void dump2(std::ostream &out, const INS_BiasEstimated<BaseINS> *ins) const {
      dump2(out, (const BaseINS *)ins);
      vec3_t &ba(const_cast<INS_BiasEstimated<BaseINS> *>(ins)->bias_accel());
      vec3_t &bg(const_cast<INS_BiasEstimated<BaseINS> *>(ins)->bias_gyro());
      out << ',' << ba.getX()      // Bias
          << ',' << ba.getY()
          << ',' << ba.getZ()
          << ',' << bg.getX()
          << ',' << bg.getY()
          << ',' << bg.getZ();
    }

    template <class BaseFINS>
    void dump2(
        std::ostream &out, const Filtered_INS_BiasEstimated<BaseFINS> *fins) const {
      dump2(out, (const BaseFINS *)fins);
      if(options.dump_stddev){
        const mat_t &P(
            const_cast<Filtered_INS_BiasEstimated<BaseFINS> *>(fins)->getFilter().getP());
        for(int i(Filtered_INS_BiasEstimated<BaseFINS>::P_SIZE_WITHOUT_BIAS), j(0);
            j < Filtered_INS_BiasEstimated<BaseFINS>::P_SIZE_BIAS; ++i, ++j){
          out << ',' << sqrt(P(i, i));
        }
      }
    }

  public:
    /**
     * print current state
     * 
     * @param itow current time
     */
    void dump(std::ostream &out) const {
      INS_GPS::dump(out);
      dump2(out, this);
    }
};

using namespace std;

class StreamProcessor
    : public AbstractSylphideProcessor<float_sylph_t> {

  public:
    static const unsigned int buffer_size;

  protected:
    Updatable *updatable;

    typedef AbstractSylphideProcessor<float_sylph_t> super_t;
    typedef A_Packet_Observer<float_sylph_t> A_Observer_t;
    typedef G_Packet_Observer<float_sylph_t> G_Observer_t;
    typedef M_Packet_Observer<float_sylph_t> M_Observer_t;

    struct Handler {
      StreamProcessor &outer;
      Handler(StreamProcessor &invoker) : outer(invoker) {}
      Handler &operator=(const Handler &another){
        return *this;
      }
    };

    /**
     * A page (ADC value)
     */
    struct AHandler : public A_Observer_t, public Handler {
      bool previous_seek_next;
      A_Packet packet_latest;
      StandardCalibration<float_sylph_t> calibration;

      AHandler(StreamProcessor &invoker) : A_Observer_t(buffer_size),
          Handler(invoker),
          packet_latest(),
          calibration() {

        previous_seek_next = A_Observer_t::ready();

        options.set_typical_calibration_specs(calibration);
      }
      ~AHandler(){}
      void operator()(const A_Observer_t &observer){
        if(!observer.validate()){return;}

        float_sylph_t itow(observer.fetch_ITOW());
        if(options.reduce_1pps_sync_error){
          float_sylph_t delta_t(itow - packet_latest.itow);
          if((delta_t >= 1) && (delta_t < 2)){itow -= 1;}
        }
        packet_latest.itow = itow;

        int ch[9];
        A_Observer_t::values_t values(observer.fetch_values());
        for(int i = 0; i < 8; i++){
          ch[i] = values.values[i];
        }
        ch[8] = values.temperature;
        packet_latest.accel = calibration.raw2accel(ch).values;
        packet_latest.omega = calibration.raw2omega(ch).values;

        Handler::outer.updatable->update(packet_latest);
      }
    } a_handler;

    /**
     * G page (u-blox)
     */
    struct GHandler : public G_Observer_t, public Handler {
      bool previous_seek_next;
      Vector3<float_sylph_t> lever_arm;
      G_Packet packet_latest;
      int itow_ms_0x0102, itow_ms_0x0112;
      int week_number;
      struct status_t {
        unsigned int gps;
        enum {
          TIME_STAMP_INVALID,
          TIME_STAMP_BEFORE_START,
          TIME_STAMP_IN_RANGE,
          TIME_STAMP_AFTER_END,
        } time_stamp;
        status_t()
            : gps(G_Observer_t::status_t::NO_FIX),
            time_stamp(TIME_STAMP_INVALID) {}
      } status;

      GHandler(StreamProcessor &invoker)
          : G_Observer_t(buffer_size),
          Handler(invoker),
          lever_arm(),
          packet_latest(),
          itow_ms_0x0102(-1), itow_ms_0x0112(-1),
          week_number(Options::gps_time_t::WN_INVALID), status() {
        previous_seek_next = G_Observer_t::ready();
        packet_latest.valid_position = packet_latest.valid_velocity = false;
      }
      ~GHandler(){}

      void update_week_number(const int &wn) {
        week_number = wn;
        if(status.time_stamp == status_t::TIME_STAMP_INVALID){
          status.time_stamp = status_t::TIME_STAMP_BEFORE_START;
        }
      }
      template <class GHandler_Packet>
      void update(const GHandler_Packet &packet){
        switch(status.time_stamp){
          case status_t::TIME_STAMP_INVALID:
          case status_t::TIME_STAMP_AFTER_END:
            return;
          case status_t::TIME_STAMP_BEFORE_START:
            if(!options.is_time_after_start(packet.itow, week_number)){
              return;
            }
            status.time_stamp = status_t::TIME_STAMP_IN_RANGE;
          case status_t::TIME_STAMP_IN_RANGE:
            if(!options.is_time_before_end(packet.itow, week_number)){
              status.time_stamp = status_t::TIME_STAMP_AFTER_END;
              return;
            }
            break;
        }
        Handler::outer.updatable->update(packet);
      }

      void update_PV(const int &itow_ms){
        packet_latest.itow = (float_sylph_t)1E-3 * itow_ms;
        if(options.gps_fake_lock){
          packet_latest.latitude = packet_latest.longitude = packet_latest.height = 0;
          packet_latest.sigma_2d = packet_latest.sigma_height = 1E+1;
          packet_latest.v_n = packet_latest.v_e = packet_latest.v_d = 0;
          packet_latest.sigma_vel = 1;
        }
        update(packet_latest);
        packet_latest.valid_position = packet_latest.valid_velocity = false; // invalidate
      }

      /**
       * Extract the following data.
       * {class, id} = {0x01, 0x02} : position
       * {class, id} = {0x01, 0x03} : status
       * {class, id} = {0x01, 0x06} : solution
       * {class, id} = {0x01, 0x12} : velocity
       */
      void check_nav(const G_Observer_t &observer, const G_Observer_t::packet_type_t &packet_type){
        switch(packet_type.mid){
          case 0x02:   // NAV-POSLLH
          case 0x14: { // NAV-HPPOSLLH

            int itow_ms;
            G_Observer_t::position_t position;
            G_Observer_t::position_acc_t position_acc;

            if(packet_type.mid == 0x14){
              // Assumption, 0x02 and 0x14 are generated before 0x12
              if((observer[6 + 3] & 0x01) != 0){return;} // invalid?
              itow_ms = observer.fetch_ITOW_ms(4);
              if(itow_ms == itow_ms_0x0102){ // when 0x0102 comes earlier
                packet_latest.valid_position = false; // accept overwrite with 0x0114
              }
              position = observer.fetch_position_hp();
              position_acc = observer.fetch_position_acc_hp();
            }else{
              itow_ms = observer.fetch_ITOW_ms();
              if(itow_ms == itow_ms_0x0102){ // when 0x0114 comes earlier
                return; // skip 0x0102.
              }
              position = observer.fetch_position();
              position_acc = observer.fetch_position_acc();
            }

            //cerr << "G_Arrive 0x02 : " << observer.fetch_ITOW() << endl;

            if(packet_latest.valid_position){ // previous position is not committed
              update_PV(itow_ms_0x0102);
            }

            itow_ms_0x0102 = itow_ms;

            packet_latest.latitude = deg2rad(position.latitude);
            packet_latest.longitude = deg2rad(position.longitude);
            packet_latest.height = position.altitude;
            packet_latest.sigma_2d = position_acc.horizontal;
            packet_latest.sigma_height = position_acc.vertical;
            packet_latest.valid_position = true;

            if(itow_ms_0x0102 == itow_ms_0x0112){ // commit position and velocity
              update_PV(itow_ms_0x0102);
            }
            return;
          }
          case 0x03: { // NAV-STATUS
            G_Observer_t::status_t st(observer.fetch_status());
            status.gps = st.fix_type;
            return;
          }
          case 0x06: { // NAV-SOL
            G_Observer_t::solution_t solution(observer.fetch_solution());
            if(solution.status_flags & G_Observer_t::solution_t::WN_VALID){
              update_week_number(solution.week);
            }
            return;
          }
          case 0x12: { // NAV-VELNED
            G_Observer_t::velocity_t
                velocity(observer.fetch_velocity());
            G_Observer_t::velocity_acc_t
                velocity_acc(observer.fetch_velocity_acc());

            //cerr << "G_Arrive 0x12 : " << current_itow << " =? " << packet.itow << endl;

            if(packet_latest.valid_velocity){ // previous velocity is not committed
              update_PV(itow_ms_0x0112);
            }

            itow_ms_0x0112 = observer.fetch_ITOW_ms();

            packet_latest.v_n = velocity.north;
            packet_latest.v_e = velocity.east;
            packet_latest.v_d = velocity.down;
            packet_latest.sigma_vel = velocity_acc.acc;
            packet_latest.valid_velocity = true;

            if(itow_ms_0x0102 == itow_ms_0x0112){ // commit position and velocity
              update_PV(itow_ms_0x0112);
            }
            return;
          }
          case 0x20: { // NAV-TIMEGPS
            TimePacket packet;
            packet.itow = observer.fetch_ITOW();
            char buf[4];
            observer.inspect(buf, sizeof(buf), 6 + 8);
            if(packet.valid_week_num = ((unsigned char)buf[3] & 0x02)){
              // valid week number
              update_week_number(packet.week_num = le_char2_2_num<unsigned short>(*buf));
              if(packet.valid_leap_sec = ((unsigned char)buf[3] & 0x04)){
                // valid UTC (leap seconds)
                packet.leap_sec = (char)(buf[2]);
              }
            }
            Handler::outer.updatable->update(packet);
            return;
          }
          default: return;
        }
      }

      /**
       * Extract the following data.
       * {class, id} = {0x02, 0x10} : raw measurement (pseudorange, carrier, doppler)
       * {class, id} = {0x02, 0x11} : subframe
       * {class, id} = {0x02, 0x31} : ephemeris
       */
      void check_rxm(const G_Observer_t &observer, const G_Observer_t::packet_type_t &packet_type){
        switch(packet_type.mid){
          case 0x10: { // RXM-RAW
            return;
          }
          case 0x11: { // RXM-SFRB
            return;
          }
          case 0x31: { // RXM-EPH
            return;
          }
          default: return;
        }
      }

      void operator()(const G_Observer_t &observer){
        if(!observer.validate()){return;}

        G_Observer_t::packet_type_t packet_type(observer.packet_type());
        switch(packet_type.mclass){
          case 0x01: check_nav(observer, packet_type); break;
          case 0x02: check_rxm(observer, packet_type); break;
        }
      }
    } g_handler;

    struct MHandler : public M_Observer_t, public Handler {
      bool previous_seek_next;
      M_Packet packet_latest;
      MHandler(StreamProcessor &invoker)
          : M_Observer_t(buffer_size),
          Handler(invoker),
          packet_latest() {
        previous_seek_next = M_Observer_t::ready();
      }
      ~MHandler(){}
      void operator()(const M_Observer_t &observer){
        if(!observer.validate()){return;}

        M_Observer_t::values_t values(observer.fetch_values());

        // Check value to remove outlier
        short *targets[] = {values.x, values.y, values.z};
        static const int threshold(200);
        for(int j(0); j < sizeof(targets) / sizeof(targets[0]); j++){
          for(int i(0); i < 3; i++){
            int diff_abs(abs(targets[j][i] - targets[j][3]));
            if((diff_abs > threshold) && (diff_abs < (4096 * 2 - threshold))){
              return;
            }
          }
        }

        float_sylph_t itow(observer.fetch_ITOW());
        if(options.reduce_1pps_sync_error){
          float_sylph_t delta_t(itow - packet_latest.itow);
          if((delta_t >= 1) && (delta_t < 2)){itow -= 1;}
        }
        packet_latest.itow = itow;

        // TODO: magnetic sensor axes must correspond to ones of accelerometer and gyro.
        packet_latest.mag[0] = values.x[3];
        packet_latest.mag[1] = values.y[3];
        packet_latest.mag[2] = values.z[3];

        Handler::outer.updatable->update(packet_latest);
      }
    } m_handler;

  protected:
    int invoked;
    istream *in;
    
  public:
    StreamProcessor()
        : super_t(), updatable(&updatable_blackhole),
        in(NULL), invoked(0),
        a_handler(*this),
        g_handler(*this),
        m_handler(*this) {

    }
    StreamProcessor(const StreamProcessor &another)
        : super_t(another), updatable(another.updatable),
        in(another.in), invoked(another.invoked),
        a_handler(*this),
        g_handler(*this),
        m_handler(*this) {
      a_handler = another.a_handler;
      g_handler = another.g_handler;
      m_handler = another.m_handler;
    }
    ~StreamProcessor(){}

    Updatable *&update_target() {
      return updatable;
    }

    const StandardCalibration<float_sylph_t> &calibration() const{
      return a_handler.calibration;
    }

    istream *&input() {
      return in;
    }

    /**
     * Process stream in units of 1 page
     * 
     * @param in stream
     * @return (bool) true when success, otherwise false.
     */
    bool process_1page(){
      char buffer[SYLPHIDE_PAGE_SIZE];
      
      int read_count;
      in->read(buffer, SYLPHIDE_PAGE_SIZE);
      read_count = static_cast<int>(in->gcount());
      if(in->fail() || (read_count == 0)){return false;}
      invoked++;
    
#if DEBUG
      cerr << "--read-- : " << invoked << " page" << endl;
      cerr << hex;
      for(int i = 0; i < read_count; i++){
        cerr 
          << setfill('0') 
          << setw(2)
          << (unsigned int)((unsigned char)buffer[i]) << ' ';
      }
      cerr << dec;
      cerr << endl;
#endif
    
      if(read_count < SYLPHIDE_PAGE_SIZE){
#if DEBUG
        cerr << "--skipped-- : " << invoked << " page ; count = " << read_count << endl;
#endif
      }

      switch(buffer[0]){
        case 'A':
          super_t::process_packet(
              buffer, read_count,
              a_handler, a_handler.previous_seek_next, a_handler);
          break;
        case 'G':
          super_t::process_packet(
              buffer, read_count,
              g_handler, g_handler.previous_seek_next, g_handler);
          if(g_handler.status.time_stamp == GHandler::status_t::TIME_STAMP_AFTER_END){ // Time check
            return false;
          }
          break;
        case 'M':
          if(!options.use_magnet){break;}
          super_t::process_packet(
              buffer, read_count,
              m_handler, m_handler.previous_seek_next, m_handler);
          break;
      }

      return true;
    }

    bool check_spec(const char *spec, const bool &dry_run = false){
      const char *value;
      if(value = Options::get_value(spec, "calib_file", false)){ // calibration file
        if(dry_run){return true;}
        return options.load_calibration_file(a_handler.calibration, value);
      }

      if(value = Options::get_value(spec, "lever_arm", false)){ // Lever Arm
        if(dry_run){return true;}
        double buf[3];
        if(std::sscanf(value, "%lf,%lf,%lf",
            &(buf[0]), &(buf[1]), &(buf[2])) != 3){
          cerr << "(error!) Lever arm option requires 3 arguments." << endl;
          return false;
        }
        for(int i(0); i < sizeof(buf) / sizeof(buf[0]); ++i){
          g_handler.lever_arm[i] = buf[i];
        }
        g_handler.packet_latest.lever_arm = &(g_handler.lever_arm);
        std::cerr << "lever_arm: " << g_handler.lever_arm << std::endl;
        return true;
      }

      return false;
    }
};

const unsigned int StreamProcessor::buffer_size = SYLPHIDE_PAGE_SIZE * 0x100;

list<StreamProcessor> processors;

template <class INS_GPS>
class INS_GPS_NAV<INS_GPS>::Helper {
  protected:
    enum {
      UNINITIALIZED,
      JUST_INITIALIZED,
      TIME_UPDATED,
      MEASUREMENT_UPDATED,
      WAITING_UPDATE,
    } status;
    INS_GPS_NAV<INS_GPS> &nav;
    const int min_a_packets_for_init; // must be greater than 0

    template <class T>
    struct PacketBuffer {
      const int max_size;
      typedef deque<T> buf_t;
      buf_t buf;
      PacketBuffer(const int &_max_size) : max_size(_max_size), buf() {}
      void push(const T &packet){
        if((int)buf.size() >= max_size){buf.pop_front();}
        buf.push_back(packet);
      }
    };

    typedef PacketBuffer<A_Packet> recent_a_t;
    recent_a_t recent_a;

    typedef PacketBuffer<M_Packet> recent_m_t;
    recent_m_t recent_m;

    vec3_t get_mag(const float_t &itow){
      if(recent_m.buf.size() < 2){
        return vec3_t(1, 0, 0); // heading is north
      }
      typename recent_m_t::buf_t::const_iterator
          it_a(nearest(recent_m.buf, itow, 2)),
          it_b(it_a + 1);
      float_t
          weight_a((it_b->itow - itow) / (it_b->itow - it_a->itow)),
          weight_b(1. - weight_a);
      /* Reduce excessive extrapolation.
       * The extrapolation is required, because M page combines several samples which are sometimes obtained late.
       * The threshold is +/- 2 steps.
       */
      if(weight_a > 3){
        weight_a = 1;
        weight_b = 0;
      }else if(weight_b > 3){
        weight_b = 1;
        weight_a = 0;
      }
      return (it_a->mag * weight_a) + (it_b->mag * weight_b);
    }
  public:
    template <class TimeStamp>
    struct TimeStampGenerator {
      void update(const TimePacket &packet){}
      TimeStamp operator()(const float_t &t, const int &wn = 0) const {
        return (TimeStamp)t;
      }
    };

    template <class FloatT>
    struct TimeStampGenerator<CalendarTimeStamp<FloatT> > {
      typedef CalendarTimeStamp<FloatT> stamp_t;
      typename stamp_t::Converter itow2calendar;
      TimeStampGenerator() : itow2calendar() {
        itow2calendar.correction_sec
            = 60 * 60 * options.time_stamp.correction_hr;
      }
      void update(const TimePacket &packet){
        packet.apply<FloatT>(itow2calendar);
      }
      stamp_t operator()(const FloatT &itow) const {
        return stamp_t(itow2calendar.convert(itow), itow);
      }
      stamp_t operator()(const FloatT &itow, const int &wn) const {
        return stamp_t(itow2calendar.convert(itow, wn), itow);
      }
    };

    TimeStampGenerator<typename INS_GPS::time_stamp_t> t_stamp_generator;

    void before_any_update(){
      if(status >= JUST_INITIALIZED){
        status = WAITING_UPDATE;
      }
    }

    void compass(const M_Packet &packet){
      recent_m.push(packet);
    }

    Helper(INS_GPS_NAV<INS_GPS> &_nav)
        : status(UNINITIALIZED), nav(_nav),
        min_a_packets_for_init(options.initial_attitude.mode == options.initial_attitude.FULL_GIVEN ? 1 : 0x10),
        recent_a(max(min_a_packets_for_init, 0x100)),
        recent_m(0x10),
        t_stamp_generator() {
    }
  
  protected:
    template <class Base_INS_GPS>
    NAV::updated_items_t updated_items(
        const INS_GPS_Back_Propagate<Base_INS_GPS> *ins_gps) const {
      NAV::updated_items_t res;

      // When smoothing is activated
      switch(status){
        case MEASUREMENT_UPDATED: {
          float_t itow(recent_a.buf.back().itow);
          typedef typename INS_GPS_Back_Propagate<Base_INS_GPS>::snapshots_t snapshots_t;
          const snapshots_t &snapshots(ins_gps->get_snapshots());
          int index(0);
          for(typename snapshots_t::const_iterator it(snapshots.begin()), it_end(snapshots.end());
              it != it_end;
              ++it, index++){
            if(it->elapsedT_from_last_correct >= options.back_propagate_property.back_propagate_depth){
              break;
            }

            if(index == 0){
              if(!options.dump_correct){continue;}
              it->ins_gps.set_header("BP_MU", t_stamp_generator(itow + it->elapsedT_from_last_correct));
              res.push_back(&(it->ins_gps));
            }else{
              if(!options.dump_update){continue;}
              it->ins_gps.set_header("BP_TU",  t_stamp_generator(itow + it->elapsedT_from_last_correct));
              res.push_back(&(it->ins_gps));
            }
          }
          break;
        }
      }

      return res;
    }

    NAV::updated_items_t updated_items(void *) const {
      NAV::updated_items_t res;

      switch(status){
        case TIME_UPDATED:
          if(!options.dump_update){break;}
          res.push_back(nav.ins_gps);
          break;
        case JUST_INITIALIZED:
        case MEASUREMENT_UPDATED:
          if(!options.dump_correct){break;}
          res.push_back(nav.ins_gps);
          break;
      }
      return res;
    }

  public:
    NAV::updated_items_t updated_items() const {
      return updated_items(nav.ins_gps);
    }

  protected:
    void time_update(const A_Packet &a_packet, float_t deltaT){

      static const int one_week(60 * 60 * 7 * 24);
      if(deltaT <= -(one_week / 2)){ // Check roll over
        deltaT += one_week;
      }

      // Check interval from the last time update
#define INTERVAL_THRESHOLD 10
      if((deltaT <= 0) || (deltaT >= INTERVAL_THRESHOLD)){
        // Skip update when discontinuity is too large.
        return;
      }

      nav.update(a_packet.accel, a_packet.omega, deltaT);
      status = TIME_UPDATED;
    }

  public:
    /**
     * Perform time update by using acceleration and angular speed obtained with accelerometer and gyro.
     * 
     * @param a_packet acceleration and angular speed
     */
    void time_update(const A_Packet &a_packet){

      if(status >= JUST_INITIALIZED){
        const A_Packet &previous(recent_a.buf.back());

        // Check interval from the last time update
        float_t deltaT(previous.interval(a_packet));
        time_update(a_packet, deltaT);
        nav.ins_gps->set_header("TU",  t_stamp_generator(a_packet.itow));
      }

      recent_a.push(a_packet);
    }

  protected:
    void time_update_after_initialization(const G_Packet &g_packet){
      typename recent_a_t::buf_t::const_reverse_iterator it_r(recent_a.buf.rbegin()), it_r_end(recent_a.buf.rend());
      for(; it_r != it_r_end; ++it_r){
        if(g_packet.interval_rollover(*it_r) <= 0){break;}
      }
      const Packet *packet(&g_packet);
      for(typename recent_a_t::buf_t::const_iterator it(it_r.base()), it_end(recent_a.buf.end()); // it_r.base() position is not it_r position!!
          it != it_end; ++it){
        time_update(*it, packet->interval(*it));
        packet = &(*it);
      }
      nav.ins_gps->set_header("MU",  t_stamp_generator(g_packet.itow));
    }

    void initialize(
        const float_t &itow,
        const float_t &latitude,
        const float_t &longitude,
        const float_t &height,
        const float_t &v_north,
        const float_t &v_east,
        const float_t &v_down){

      float_t
          yaw(deg2rad(options.initial_attitude.yaw_deg)),
          pitch(deg2rad(options.initial_attitude.pitch_deg)),
          roll(deg2rad(options.initial_attitude.roll_deg));

      while(options.initial_attitude.mode < options.initial_attitude.FULL_GIVEN){
        // Estimate initial attitude by using accelerometer and magnetic sensor (if available) under static assumption

        // Normalization
        vec3_t acc(0, 0, 0);
        for(typename recent_a_t::buf_t::iterator it(recent_a.buf.begin()), it_end(recent_a.buf.end());
            it != it_end;
            ++it){
          acc += it->accel;
        }
        acc /= recent_a.buf.size();
        vec3_t acc_reg(-acc / acc.abs());

        // Estimate roll angle
        roll = atan2(acc_reg[1], acc_reg[2]);
        if(options.initial_attitude.mode >= options.initial_attitude.YAW_PITCH){break;}

        // Estimate pitch angle
        pitch = -asin(acc_reg[0]);
        if(options.initial_attitude.mode >= options.initial_attitude.YAW_ONLY){break;}

        // Estimate yaw when magnetic compass is available
        if(!recent_m.buf.empty()){
          yaw = nav.get_mag_yaw(get_mag(itow), pitch, roll,
              latitude, longitude, height);
        }
        break;
      }

      status = JUST_INITIALIZED;

      cerr << "Init : " << setprecision(10) << itow << endl;
      cerr << "Initial attitude (yaw, pitch, roll) [deg]: "
          << rad2deg(yaw) << ", "
          << rad2deg(pitch) << ", "
          << rad2deg(roll) << endl;

      nav.ins_gps->initPosition(latitude, longitude, height);
      nav.ins_gps->initVelocity(v_north, v_east, v_down);
      nav.ins_gps->initAttitude(yaw, pitch, roll);

      options.dump_relative.set_base(latitude, longitude);

      for(char buf[0x4000]; !options.init_misc->eof(); ){ // Miscellaneous setup
        options.init_misc->getline(buf, sizeof(buf));
        if(!nav.init_misc(buf)){
          cerr << "(error!) Initialization failure: " << buf << endl;
          exit(-1);
        }
      }
    }

    void time_update_before_measurement_update(const float_t &advanceT, void *){
      if(advanceT <= 0){return;}
      // Time update up to the GPS observation
      time_update(recent_a.buf.back(), advanceT);
    }

    template <class Base_INS_GPS>
    void time_update_before_measurement_update(const float_t &advanceT, INS_GPS_RealTime<Base_INS_GPS> *){
      return;
    }

    bool check_time_synchronization(const Packet &packet) const {
      if(recent_a.buf.empty()){return false;}
      float_t
          delta_base(recent_a.buf.front().interval_rollover(recent_a.buf.back())), // a.newest - a.oldest
          delta(recent_a.buf.back().interval_rollover(packet)); // packet - a.newest
      return (delta_base >= 0) // newest > oldest
          && (delta_base <= recent_a.buf.size()) // A packet frequency is expected to be larger than 1 Hz
          && ((delta < 0)
            ? (-(delta_base + 5) <= delta)  // Case packet, then a.newest; most cases are applicable
            : (10 >= delta));   // Case a.newest, then packet;
    }

  public:
    /**
     * Perform measurement update by using position and velocity obtained with GPS receiver.
     * 
     * @param g_packet observation data of GPS receiver
     */
    void measurement_update(const G_Packet &g_packet){

      if(g_packet.sigma_2d >= options.gps_threshold.cont_acc_2d){ // When estimated accuracy is too big, skip.
        return;
      }
      if(status >= JUST_INITIALIZED){
        cerr << "MU : " << setprecision(10) << g_packet.itow << endl;
        
        // calculate GPS data timing;
        // negative(realtime mode, delayed), or slightly positive(other modes, because of already sorted)
        float_t gps_advance(recent_a.buf.back().interval(g_packet));
        time_update_before_measurement_update(gps_advance, nav.ins_gps);

        if(g_packet.lever_arm){ // When use lever arm effect.
          vec3_t omega_b2i_4n;
          int packets_for_mean(0x10), i(0);
          typename recent_a_t::buf_t::const_iterator it(
              nearest(recent_a.buf, g_packet.itow, packets_for_mean));
          for(; (i < packets_for_mean) && (it != recent_a.buf.end()); i++, it++){
            omega_b2i_4n += it->omega;
          }
          omega_b2i_4n /= i;
          nav.correct(
              g_packet,
              *g_packet.lever_arm,
              omega_b2i_4n,
              gps_advance);
        }else{ // When do not use lever arm effect.
          nav.correct(
              g_packet,
              gps_advance);
        }
        if(!recent_m.buf.empty()){ // When magnetic sensor is activated, try to perform yaw compensation
          if((options.yaw_correct_with_mag_when_speed_less_than_ms > 0)
              && (pow(g_packet.v_n, 2) + pow(g_packet.v_e, 2)) < pow(options.yaw_correct_with_mag_when_speed_less_than_ms, 2)){
            nav.correct_yaw(nav.get_mag_delta_yaw(get_mag(g_packet.itow), *(nav.ins_gps)));
          }
        }
        status = MEASUREMENT_UPDATED;
        nav.ins_gps->set_header("MU");
      }else if(((int)recent_a.buf.size() >= min_a_packets_for_init)
          && check_time_synchronization(g_packet) // time synchronization check
          && (g_packet.sigma_2d <= options.gps_threshold.init_acc_2d)
          && (g_packet.sigma_height <= options.gps_threshold.init_acc_v)){

        /*
         * Filter is activated when the estimate error in horizontal and vertical positions are under 20 and 10 meters, respectively.
         */
        initialize(
            g_packet.itow,
            g_packet.latitude, g_packet.longitude, g_packet.height,
            g_packet.v_n, g_packet.v_e, g_packet.v_d);
        time_update_after_initialization(g_packet);
      }
    }
};

class NAV_Generator {
  private:
    template <class T>
    static NAV *anchor(){
      return INS_GPS_NAV_Factory<typename T::product>::get_nav(processors.front().calibration());
    }
    template <class T>
    static NAV *check_bias(){
      return options.est_bias ? anchor<typename T::template bias<> >() : anchor<T>();
    }
    template <class T>
    static NAV *check_udkf(){
      return options.use_udkf
          ? check_bias<typename T::template kf<KalmanFilterUD> >()
          : check_bias<typename T::template kf<KalmanFilter> >();
    }
    template <class T>
    static NAV *check_egm(){
      return options.use_egm ? check_udkf<typename T::template egm<> >() : check_udkf<T>();
    }
  public:
    static NAV *generate(){
      switch(options.time_stamp.mode){
        case Options::time_stamp_t::CALENDAR_TIME:
          return check_egm<INS_GPS_Factory<
              INS_NAVData<INS<float_sylph_t>, CalendarTimeStamp<float_sylph_t> > > >();
        case Options::time_stamp_t::ITOW:
        default:
          return check_egm<INS_GPS_Factory<
              INS_NAVData<INS<float_sylph_t> > > >();
      }
    }
};

void loop(){
  struct NAV_Manager {
    NAV *nav;
    NAV_Manager() : nav(NAV_Generator::generate()){}
    ~NAV_Manager(){
      delete nav;
    }
  } nav_manager;
  
  nav_manager.nav->label(options.out());

  // TODO multiple log stream will be support.
  StreamProcessor &proc(processors.front());
  if(options.ins_gps_sync_strategy == Options::INS_GPS_SYNC_REALTIME){
    // Realtime mode supports only one stream.
    proc.update_target() = nav_manager.nav;
    while(proc.process_1page());
    return;
  }

  struct buffer_t : public Updatable {
    typedef deque<const Packet *> packet_pool_t;
    packet_pool_t packet_pool;
    NAV &nav;
    void sort_and_apply(int packets){
      stable_sort(packet_pool.begin(), packet_pool.end(), Packet::compare_rollover);
      while(packets-- > 0){
        packet_pool_t::reference front(packet_pool.front());
        front->apply(nav);
        delete front;
        packet_pool.pop_front();
      }
    }
    void sort_and_apply2 () {
      if(packet_pool.size() < 0x200){return;}
      sort_and_apply(0x100);
    }
    buffer_t(NAV &_nav) : packet_pool(), nav(_nav) {}
    ~buffer_t() {
      sort_and_apply(packet_pool.size());
    }
#define update_func(type) \
virtual void update(const type &packet){ \
  packet_pool.push_back(new type(packet)); \
  sort_and_apply2(); \
}
    update_func(A_Packet);
    update_func(G_Packet);
    update_func(M_Packet);
    update_func(TimePacket);
#undef update_func
  } buffer(*nav_manager.nav);
  proc.update_target() = &buffer;

  while(proc.process_1page());
}
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
